stdlogicvector/modularCamera_hw/Sensor_HallArray_Ctrl.brd

## EAGLE design Sensor_HallArray_Ctrl.brd (2026-06-28)

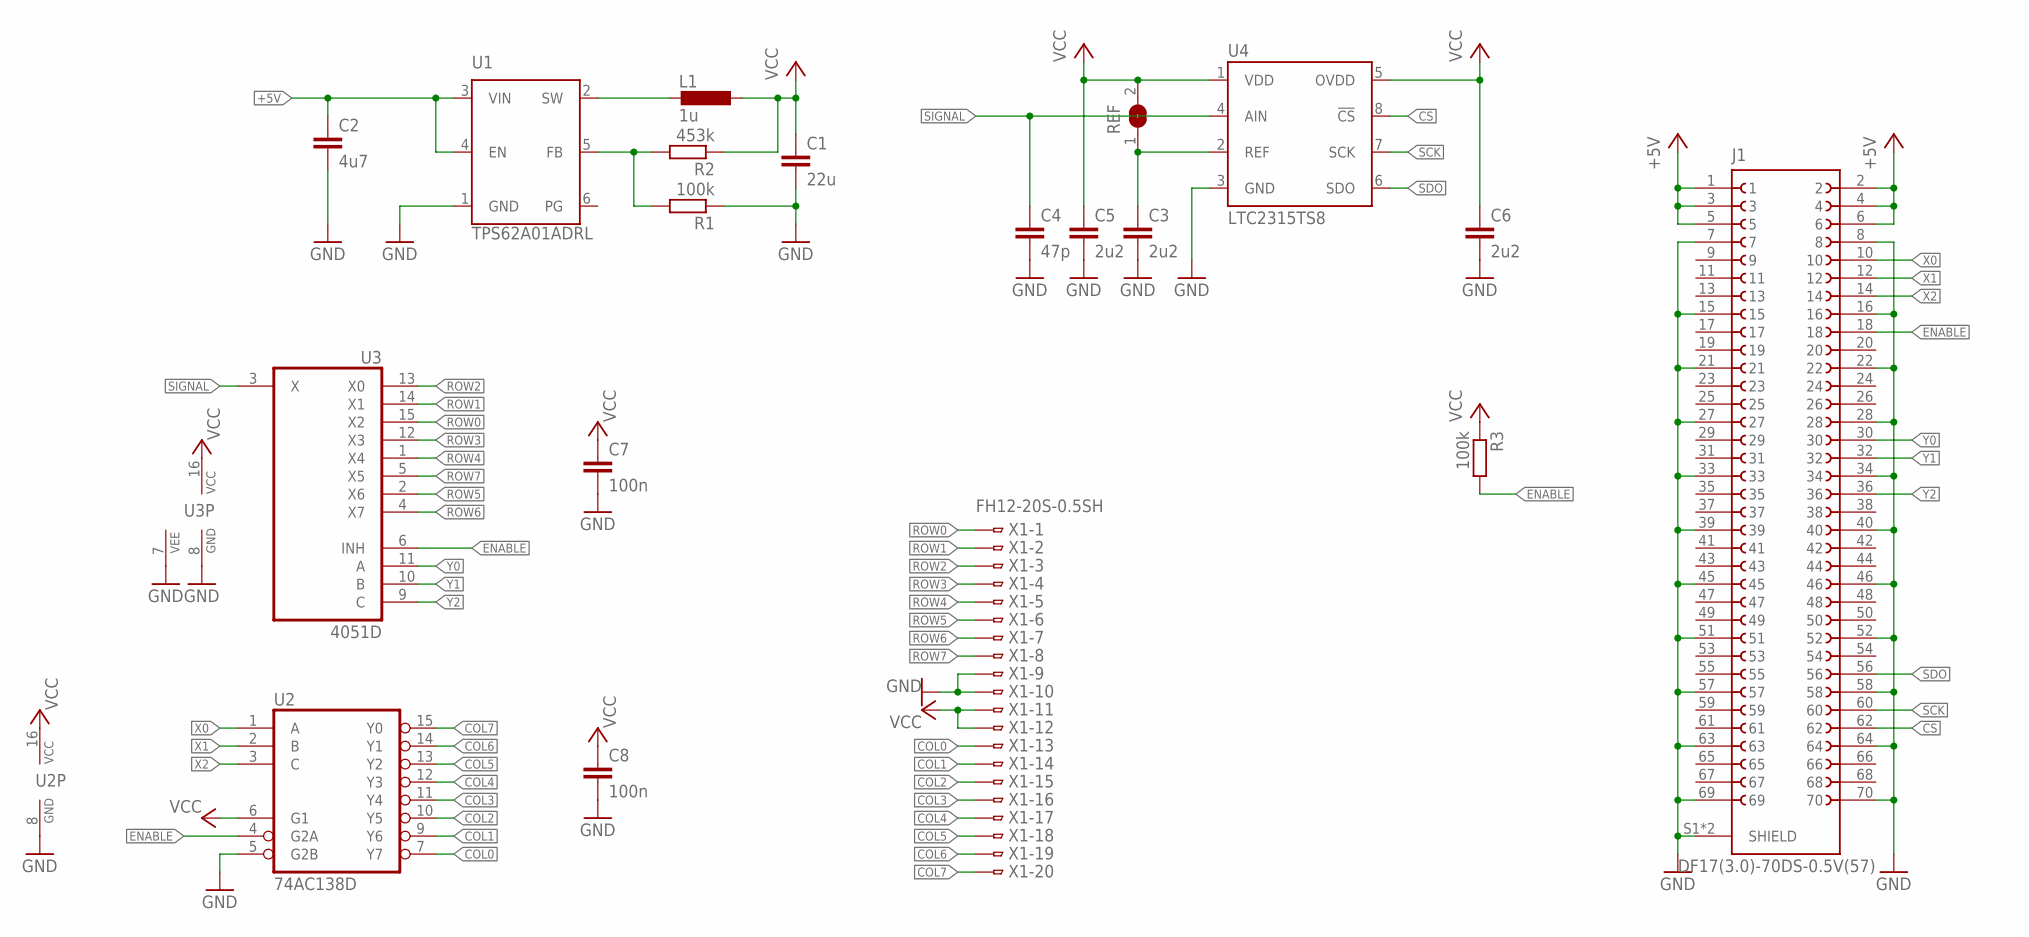
[picture p45: schematic Sensor_HallArray_Ctrl.sch]

Parts:
C1: 22u; C0603; LCSC C109448
C2: 4u7; C0603; LCSC C19666
C3, C5, C6: 2u2; C0603; LCSC C19666
C4: 47p; C0402
C7, C8: 100n; C0402
J1: DF17(3.0)-70DS-0.5V(57)
L1: 1u; L1008; MPN LQM2HPN1R0MG0L; DIGIKEY 490-5112-1-ND
R1, R3: 100k; R0402; DIGIKEY RMCF0402FT100KCT-ND
R2: 453k; R0402; LCSC C137978
REF: SJ
U1: TPS62A01ADRL; SOTFL50P160X60-6N; DIGIKEY 296-TPS62A01ADRLRCT-ND
U2: 74AC138D; SO16
U3: 4051D; SO16
U4: LTC2315TS8; SOT23-8L
X1: FH12-20S-0.5SH

Connections:
!CS: J1.62, U4.8 (!CS)
!ENABLE: J1.18, R3.2, U2.4 (G2A), U3.6 (INH)
+5V: C2.1, J1.1, J1.2, J1.3, J1.4, J1.5, J1.6, U1.3 (VIN), U1.4 (EN)
COL0: U2.7 (Y7), X1.13
COL1: U2.9 (Y6), X1.14
COL2: U2.10 (Y5), X1.15
COL3: U2.11 (Y4), X1.16
COL4: U2.12 (Y3), X1.17
COL5: U2.13 (Y2), X1.18
COL6: U2.14 (Y1), X1.19
COL7: U2.15 (Y0), X1.20
GND: C1.2, C2.2, C3.2, C4.2, C5.2, C6.2, C7.2, C8.2, J1.7, J1.8, J1.15, J1.16, J1.21, J1.22, J1.27, J1.28, J1.33, J1.34, J1.39, J1.40, J1.45, J1.46, J1.51, J1.52, J1.57, J1.58, J1.63, J1.64, J1.69, J1.70, J1.S1 (SHIELD), J1.S2 (SHIELD), R1.1, U1.1 (GND), U2.5 (G2B), U2.8 (GND), U3.7 (VEE), U3.8 (GND), U4.3 (GND), X1.9, X1.10
unnamed: R1.2, R2.2, U1.5 (FB)
unnamed: L1.2, U1.2 (SW)
unnamed: C3.1, REF.1, U4.2 (REF)
ROW0: U3.15 (X2), X1.1
ROW1: U3.14 (X1), X1.2
ROW2: U3.13 (X0), X1.3
ROW3: U3.12 (X3), X1.4
ROW4: U3.1 (X4), X1.5
ROW5: U3.2 (X6), X1.6
ROW6: U3.4 (X7), X1.7
ROW7: U3.5 (X5), X1.8
SCK: J1.60, U4.7 (SCK)
SDO: J1.56, U4.6 (SDO)
SIGNAL: C4.1, U3.3 (X), U4.4 (AIN)
VCC: C1.1, C5.1, C6.1, C7.1, C8.1, L1.1, R2.1, R3.1, REF.2, U2.6 (G1), U2.16 (VCC), U3.16 (VCC), U4.1 (VDD), U4.5 (OVDD), X1.11, X1.12
X0: J1.10, U2.1 (A)
X1: J1.12, U2.2 (B)
X2: J1.14, U2.3 (C)
Y0: J1.30, U3.11 (A)
Y1: J1.32, U3.10 (B)
Y2: J1.36, U3.9 (C)

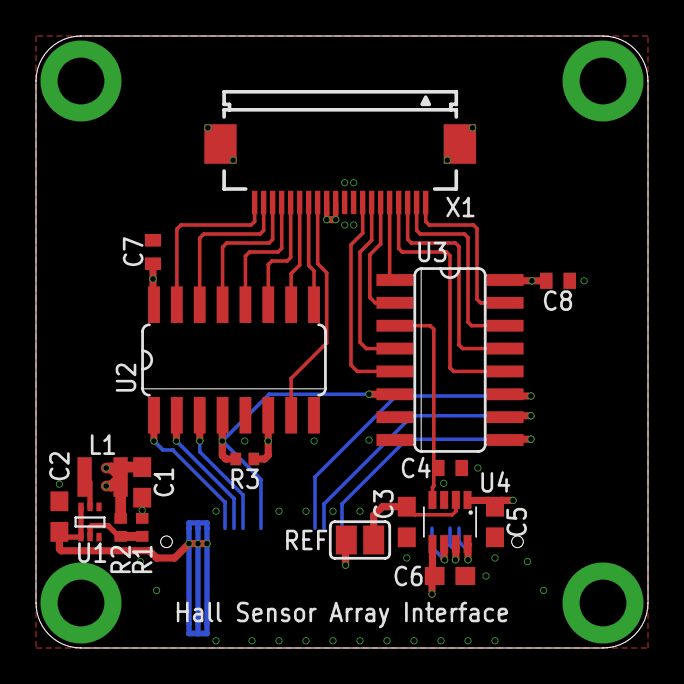
[picture p46: board Sensor_HallArray_Ctrl.brd from above]

Board: 4 copper layers, 34.0 x 34.0 mm, 19 parts (1 on the bottom side), 33 nets.
