stdlogicvector/modularCamera_hw/Sensor_Cameralink_TRX.brd

## EAGLE design Sensor_Cameralink_TRX.brd (2026-06-28)

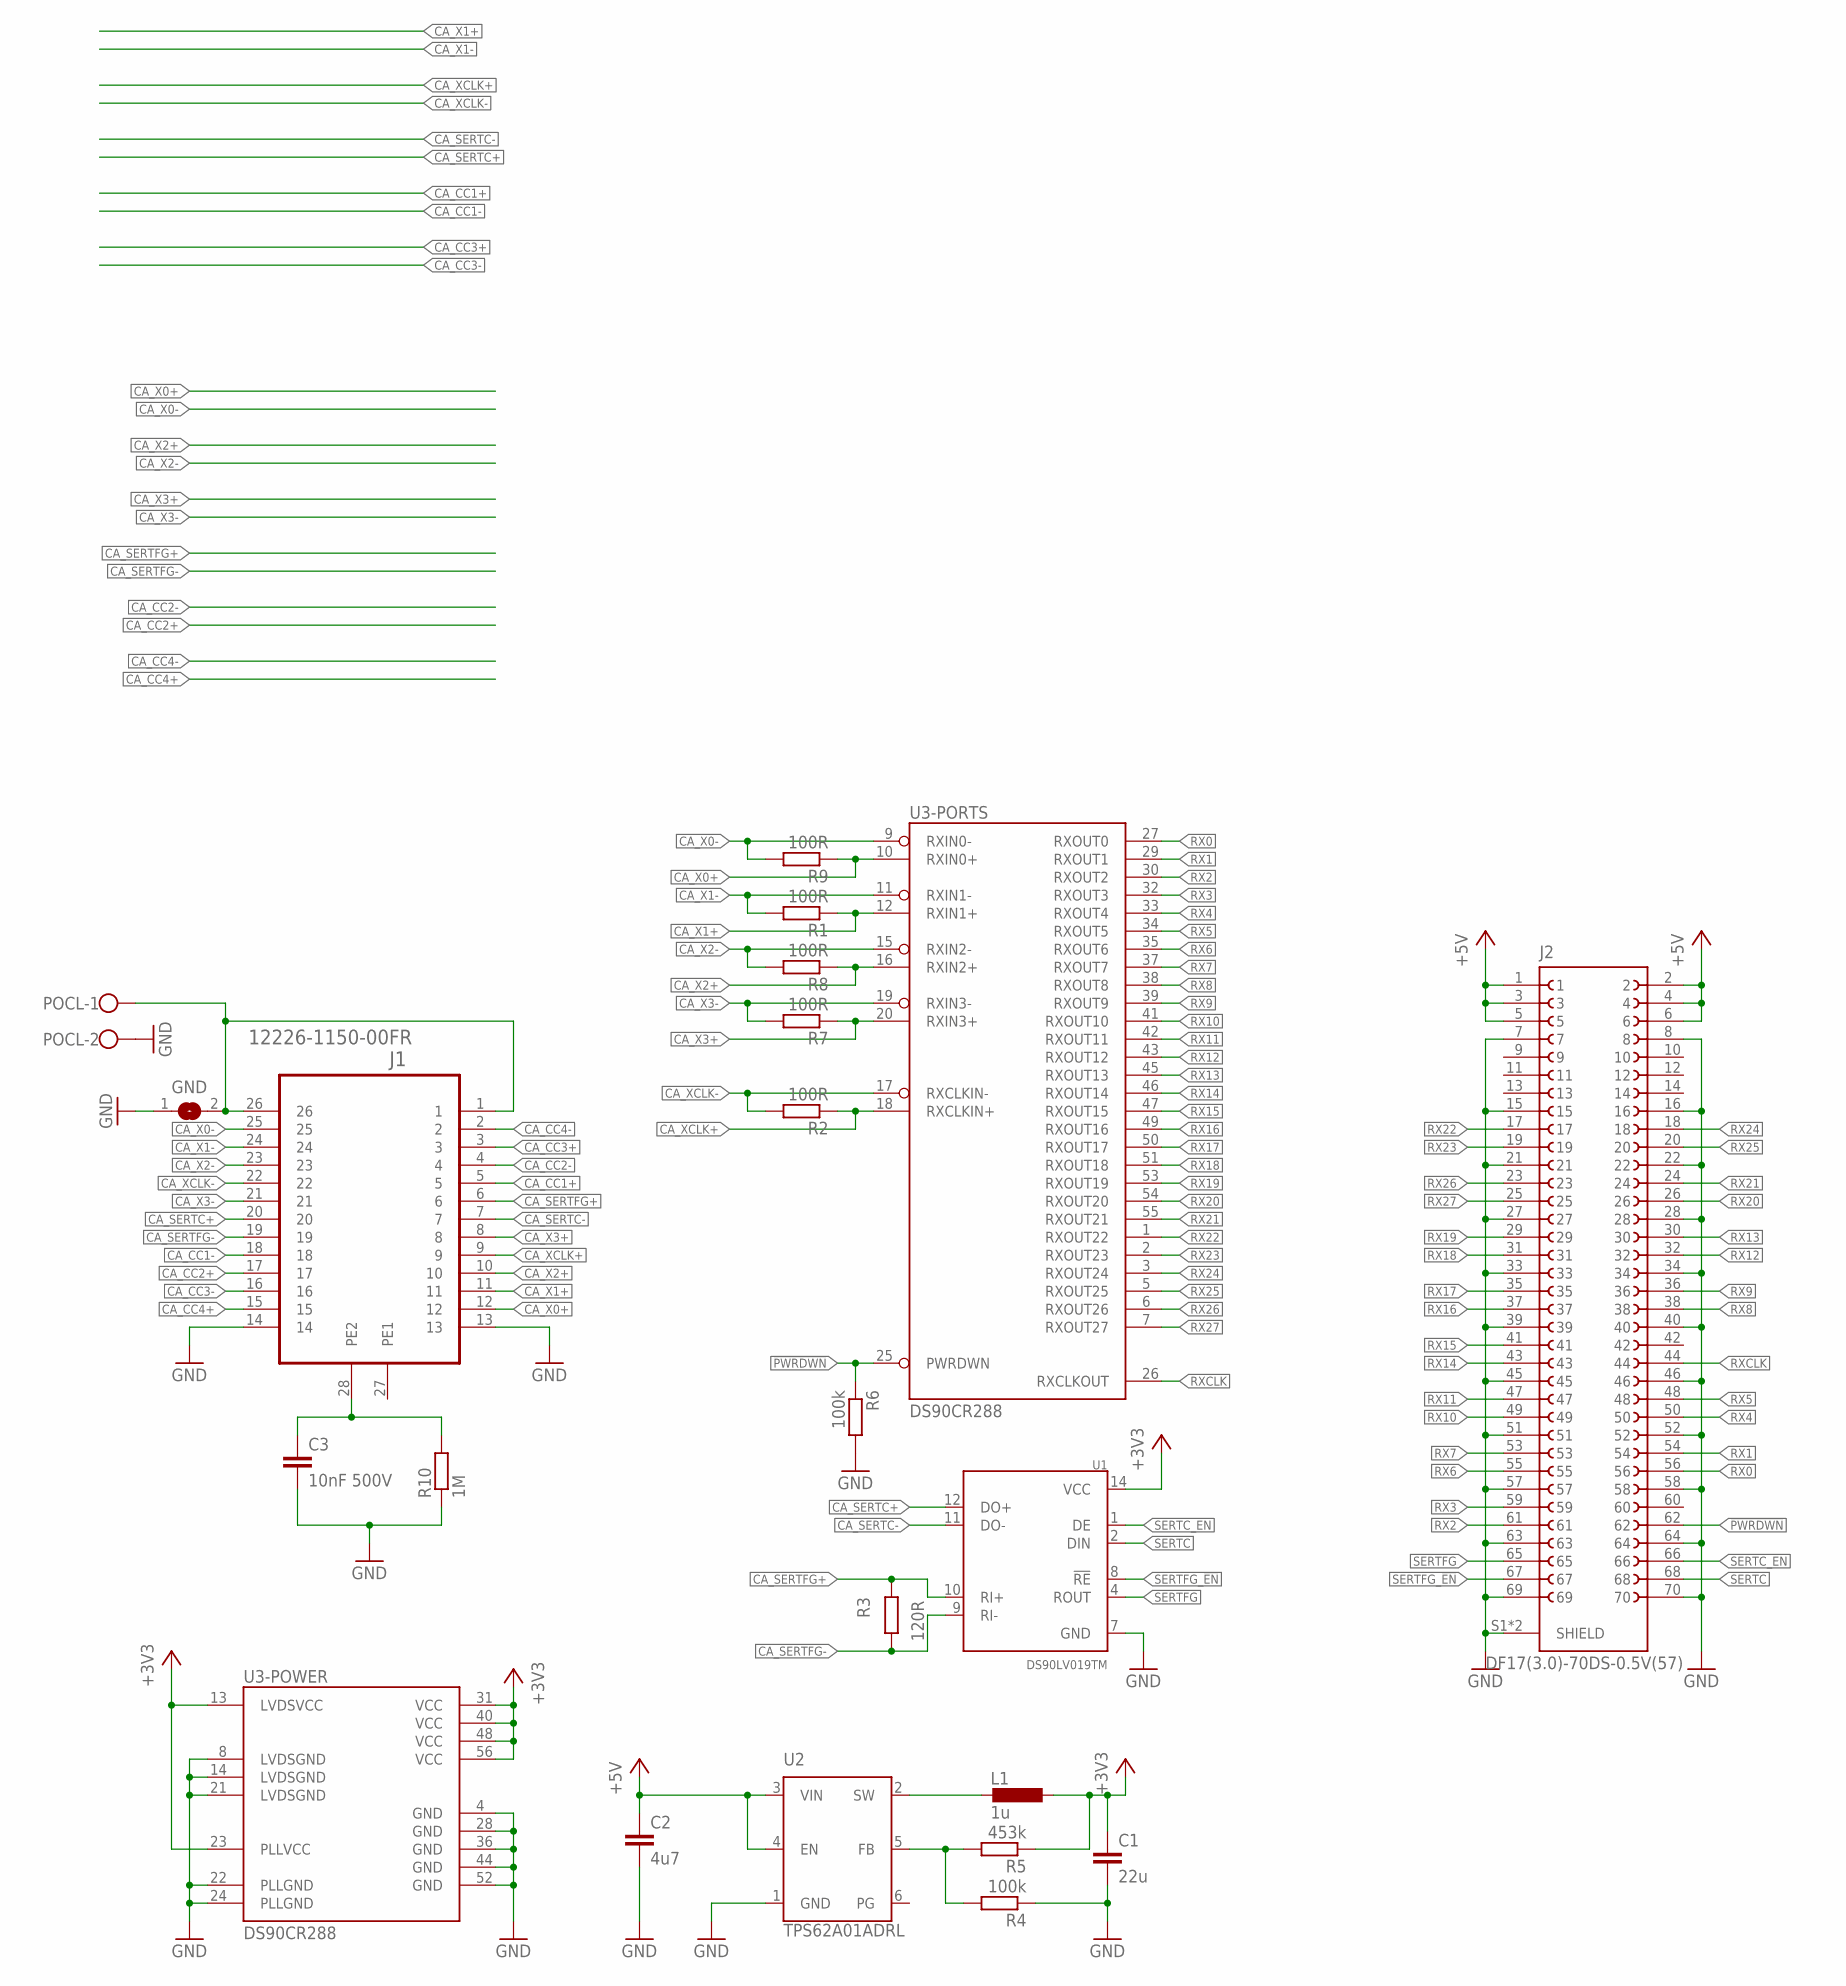
[picture p47: schematic Sensor_Cameralink_TRX.sch]

Parts:
C1: 22u; C0603; LCSC C109448
C2: 4u7; C0603; LCSC C19666
C3: 10nF 500V; C0805
GND: SJ
J1: 12226-1150-00FR; 3M_12226-1150-00FR
J2: DF17(3.0)-70DS-0.5V(57)
L1: 1u; L1008; MPN LQM2HPN1R0MG0L; DIGIKEY 490-5112-1-ND
POCL: W237-102
R1, R2, R7, R8, R9: 100R; R0402
R3: 120R; R0402
R4, R6: 100k; R0402; DIGIKEY RMCF0402FT100KCT-ND
R5: 453k; R0402; LCSC C137978
R10: 1M; R0805
U1: DS90LV019TM; SO-14
U2: TPS62A01ADRL; SOTFL50P160X60-6N; DIGIKEY 296-TPS62A01ADRLRCT-ND
U3: DS90CR288; HTSSOP56

Connections:
!PWRDWN: J2.62, R6.1, U3.25 (PWRDWN)
+3V3: C1.1, L1.1, R5.1, U1.14 (VCC), U3.13 (LVDSVCC), U3.23 (PLLVCC), U3.31 (VCC), U3.40 (VCC), U3.48 (VCC), U3.56 (VCC)
+5V: C2.1, J2.1, J2.2, J2.3, J2.4, J2.5, J2.6, U2.3 (VIN), U2.4 (EN)
CA_CC1+: J1.5
CA_CC1-: J1.18
CA_CC2+: J1.17
CA_CC2-: J1.4
CA_CC3+: J1.3
CA_CC3-: J1.16
CA_CC4+: J1.15
CA_CC4-: J1.2
CA_SERTC+: J1.20, U1.12 (DO+)
CA_SERTC-: J1.7, U1.11 (DO-)
CA_SERTFG+: J1.6, R3.1, U1.10 (RI+)
CA_SERTFG-: J1.19, R3.2, U1.9 (RI-)
CA_X0+: J1.12, R9.1, U3.10 (RXIN0+)
CA_X0-: J1.25, R9.2, U3.9 (RXIN0-)
CA_X1+: J1.11, R1.1, U3.12 (RXIN1+)
CA_X1-: J1.24, R1.2, U3.11 (RXIN1-)
CA_X2+: J1.10, R8.1, U3.16 (RXIN2+)
CA_X2-: J1.23, R8.2, U3.15 (RXIN2-)
CA_X3+: J1.8, R7.1, U3.20 (RXIN3+)
CA_X3-: J1.21, R7.2, U3.19 (RXIN3-)
CA_XCLK+: J1.9, R2.1, U3.18 (RXCLKIN+)
CA_XCLK-: J1.22, R2.2, U3.17 (RXCLKIN-)
GND: C1.2, C2.2, C3.2, GND.1, J1.13, J1.14, J2.7, J2.8, J2.15, J2.16, J2.21, J2.22, J2.27, J2.28, J2.33, J2.34, J2.39, J2.40, J2.45, J2.46, J2.51, J2.52, J2.57, J2.58, J2.63, J2.64, J2.69, J2.70, J2.S1 (SHIELD), J2.S2 (SHIELD), POCL.2, R4.1, R6.2, R10.1, U1.7 (GND), U2.1 (GND), U3.4 (GND), U3.8 (LVDSGND), U3.14 (LVDSGND), U3.21 (LVDSGND), U3.22 (PLLGND), U3.24 (PLLGND), U3.28 (GND), U3.36 (GND), U3.44 (GND), U3.52 (GND)
unnamed: C3.1, J1.28 (PE2), R10.2
unnamed: GND.2, J1.1, J1.26, POCL.1
unnamed: R4.2, R5.2, U2.5 (FB)
unnamed: L1.2, U2.2 (SW)
RX0: J2.56, U3.27 (RXOUT0)
RX1: J2.54, U3.29 (RXOUT1)
RX2: J2.61, U3.30 (RXOUT2)
RX3: J2.59, U3.32 (RXOUT3)
RX4: J2.50, U3.33 (RXOUT4)
RX5: J2.48, U3.34 (RXOUT5)
RX6: J2.55, U3.35 (RXOUT6)
RX7: J2.53, U3.37 (RXOUT7)
RX8: J2.38, U3.38 (RXOUT8)
RX9: J2.36, U3.39 (RXOUT9)
RX10: J2.49, U3.41 (RXOUT10)
RX11: J2.47, U3.42 (RXOUT11)
RX12: J2.32, U3.43 (RXOUT12)
RX13: J2.30, U3.45 (RXOUT13)
RX14: J2.43, U3.46 (RXOUT14)
RX15: J2.41, U3.47 (RXOUT15)
RX16: J2.37, U3.49 (RXOUT16)
RX17: J2.35, U3.50 (RXOUT17)
RX18: J2.31, U3.51 (RXOUT18)
RX19: J2.29, U3.53 (RXOUT19)
RX20: J2.26, U3.54 (RXOUT20)
RX21: J2.24, U3.55 (RXOUT21)
RX22: J2.17, U3.1 (RXOUT22)
RX23: J2.19, U3.2 (RXOUT23)
RX24: J2.18, U3.3 (RXOUT24)
RX25: J2.20, U3.5 (RXOUT25)
RX26: J2.23, U3.6 (RXOUT26)
RX27: J2.25, U3.7 (RXOUT27)
RXCLK: J2.44, U3.26 (RXCLKOUT)
SERTC: J2.68, U1.2 (DIN)
SERTC_EN: J2.66, U1.1 (DE)
SERTFG: J2.65, U1.4 (ROUT)
SERTFG_!EN: J2.67, U1.8 (!RE)

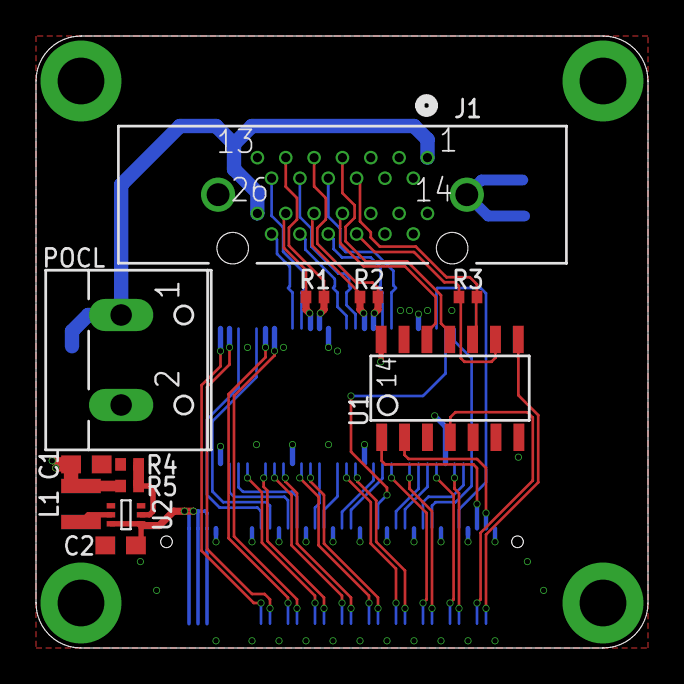
[picture p48: board Sensor_Cameralink_TRX.brd from above]

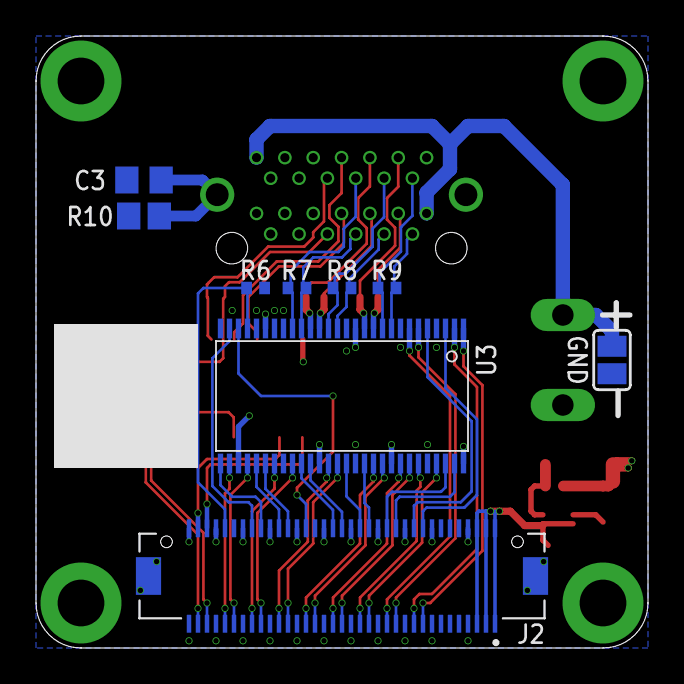
[picture p49: board Sensor_Cameralink_TRX.brd from below]

Board: 4 copper layers, 34.0 x 34.0 mm, 21 parts (9 on the bottom side), 55 nets.
