stdlogicvector/modularCamera_hw/Sensor_MT9P.brd

## EAGLE design Sensor_MT9P.brd (2026-06-28)

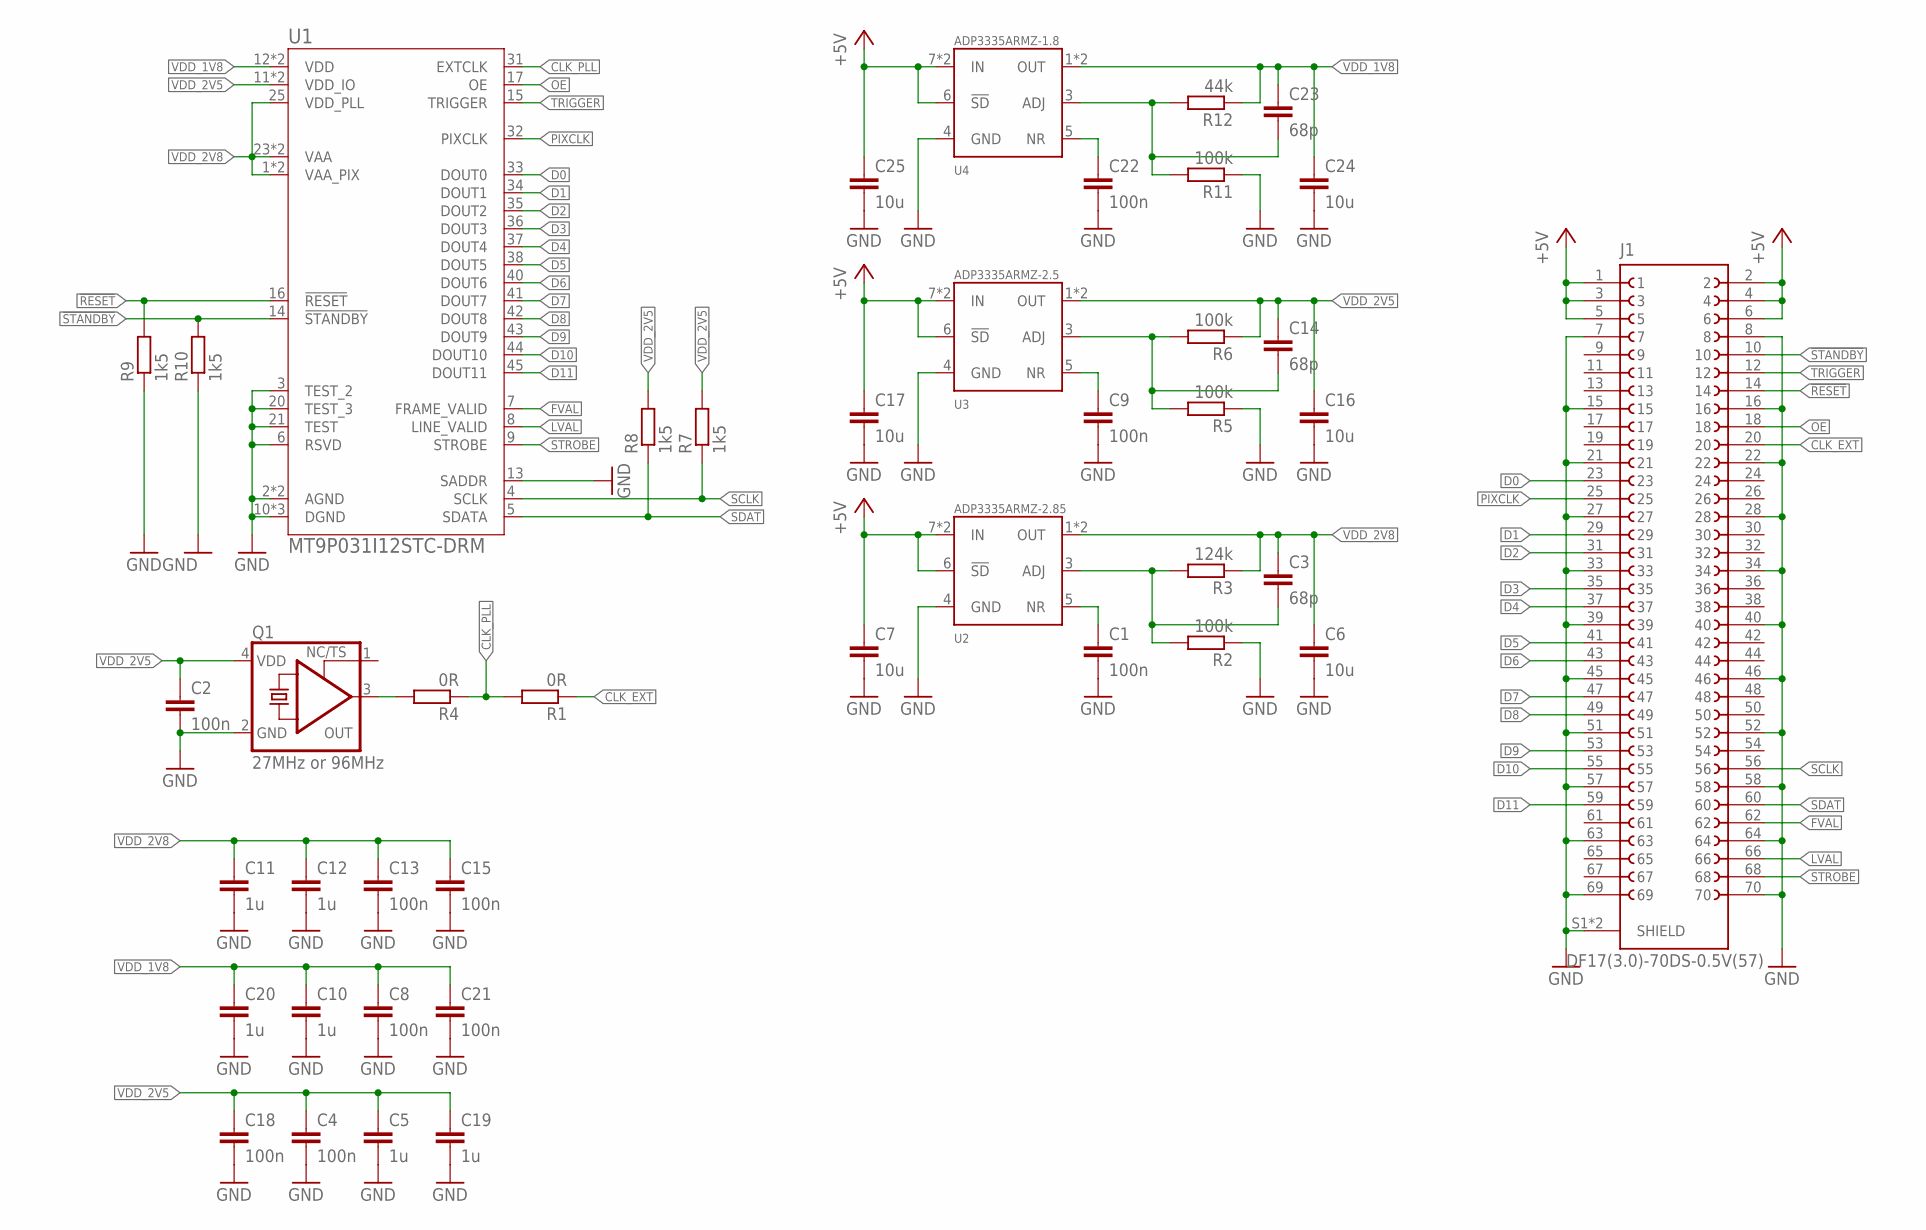
[picture p50: schematic Sensor_MT9P.sch]

Parts:
C1, C2, C4, C8, C9, C13, C15, C18, C21, C22: 100n; C0402; LCSC C1525
C3, C14, C23: 68p; C0402; LCSC C1525
C5, C10, C11, C12, C19, C20: 1u; C0402
C6, C7, C16, C17, C24, C25: 10u; C0603
J1: DF17(3.0)-70DS-0.5V(57)
Q1: 27MHz or 96MHz; 3.2X2.5_KXO-V96
R1, R4: 0R; R0402
R2, R5, R6, R11: 100k; R0402
R3: 124k; R0402
R7, R8, R9, R10: 1k5; R0402
R12: 44k; R0402
U1: MT9P031I12STC-DRM; ILCC48_10X10_847AA-O_OSI-M
U2: ADP3335ARMZ-2.85; MSOP08; DIGIKEY 505-ADP3335ARMZ-3.3RL7CT-ND
U3: ADP3335ARMZ-2.5; MSOP08; DIGIKEY 505-ADP3335ARMZ-2.5-RLCT-ND
U4: ADP3335ARMZ-1.8; MSOP08; DIGIKEY 505-ADP3335ARMZ-1.8-R7CT-ND

Connections:
!RESET: J1.14, R9.2, U1.16 (!RESET)
!STANDBY: J1.10, R10.2, U1.14 (!STANDBY)
+5V: C7.1, C17.1, C25.1, J1.1, J1.2, J1.3, J1.4, J1.5, J1.6, U2.6 (!SD), U2.7 (IN), U2.8 (IN), U3.6 (!SD), U3.7 (IN), U3.8 (IN), U4.6 (!SD), U4.7 (IN), U4.8 (IN)
CLK: Q1.3 (OUT), R4.2
CLK_EXT: J1.20, R1.1
CLK_PLL: R1.2, R4.1, U1.31 (EXTCLK)
D0: J1.23, U1.33 (DOUT0)
D1: J1.29, U1.34 (DOUT1)
D2: J1.31, U1.35 (DOUT2)
D3: J1.35, U1.36 (DOUT3)
D4: J1.37, U1.37 (DOUT4)
D5: J1.41, U1.38 (DOUT5)
D6: J1.43, U1.40 (DOUT6)
D7: J1.47, U1.41 (DOUT7)
D8: J1.49, U1.42 (DOUT8)
D9: J1.53, U1.43 (DOUT9)
D10: J1.55, U1.44 (DOUT10)
D11: J1.59, U1.45 (DOUT11)
FVAL: J1.62, U1.7 (FRAME_VALID)
GND: C1.2, C2.2, C4.2, C5.2, C6.2, C7.2, C8.2, C9.2, C10.2, C11.2, C12.2, C13.2, C15.2, C16.2, C17.2, C18.2, C19.2, C20.2, C21.2, C22.2, C24.2, C25.2, J1.7, J1.8, J1.15, J1.16, J1.21, J1.22, J1.27, J1.28, J1.33, J1.34, J1.39, J1.40, J1.45, J1.46, J1.51, J1.52, J1.57, J1.58, J1.63, J1.64, J1.69, J1.70, J1.S1 (SHIELD), J1.S2 (SHIELD), Q1.2 (GND), R2.1, R5.1, R9.1, R10.1, R11.1, U1.2 (AGND), U1.3 (TEST_2), U1.6 (RSVD), U1.10 (DGND), U1.13 (SADDR), U1.20 (TEST_3), U1.21 (TEST), U1.22 (AGND), U1.26 (DGND), U1.46 (DGND), U2.4 (GND), U3.4 (GND), U4.4 (GND)
LVAL: J1.66, U1.8 (LINE_VALID)
unnamed: C1.1, U2.5 (NR)
unnamed: C22.1, U4.5 (NR)
unnamed: C9.1, U3.5 (NR)
unnamed: C23.2, R11.2, R12.2, U4.3 (ADJ)
unnamed: C14.2, R5.2, R6.2, U3.3 (ADJ)
unnamed: C3.2, R2.2, R3.2, U2.3 (ADJ)
OE: J1.18, U1.17 (OE)
PIXCLK: J1.25, U1.32 (PIXCLK)
SCLK: J1.56, R7.1, U1.4 (SCLK)
SDAT: J1.60, R8.1, U1.5 (SDATA)
STROBE: J1.68, U1.9 (STROBE)
TRIGGER: J1.12, U1.15 (TRIGGER)
VDD_1V8: C8.1, C10.1, C20.1, C21.1, C23.1, C24.1, R12.1, U1.12 (VDD), U1.47 (VDD), U4.1 (OUT), U4.2 (OUT)
VDD_2V5: C2.1, C4.1, C5.1, C14.1, C16.1, C18.1, C19.1, Q1.4 (VDD), R6.1, R7.2, R8.2, U1.11 (VDD_IO), U1.39 (VDD_IO), U3.1 (OUT), U3.2 (OUT)
VDD_2V8: C3.1, C6.1, C11.1, C12.1, C13.1, C15.1, R3.1, U1.1 (VAA_PIX), U1.23 (VAA), U1.24 (VAA), U1.25 (VDD_PLL), U1.48 (VAA_PIX), U2.1 (OUT), U2.2 (OUT)

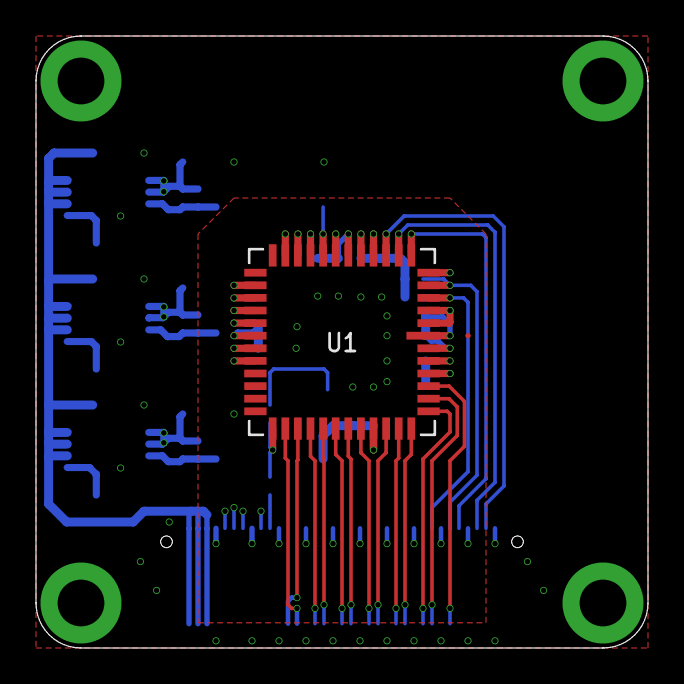
[picture p51: board Sensor_MT9P.brd from above]

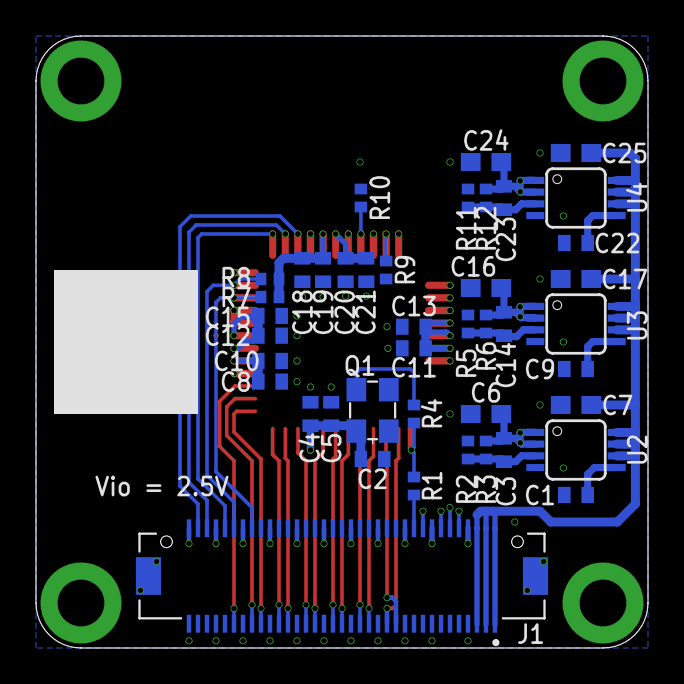
[picture p52: board Sensor_MT9P.brd from below]

Board: 4 copper layers, 34.0 x 34.0 mm, 43 parts (42 on the bottom side), 36 nets.
