stdlogicvector/modularCamera_hw/Sensor_AnalogVideo.brd

## EAGLE design Sensor_AnalogVideo.brd (2026-06-28)

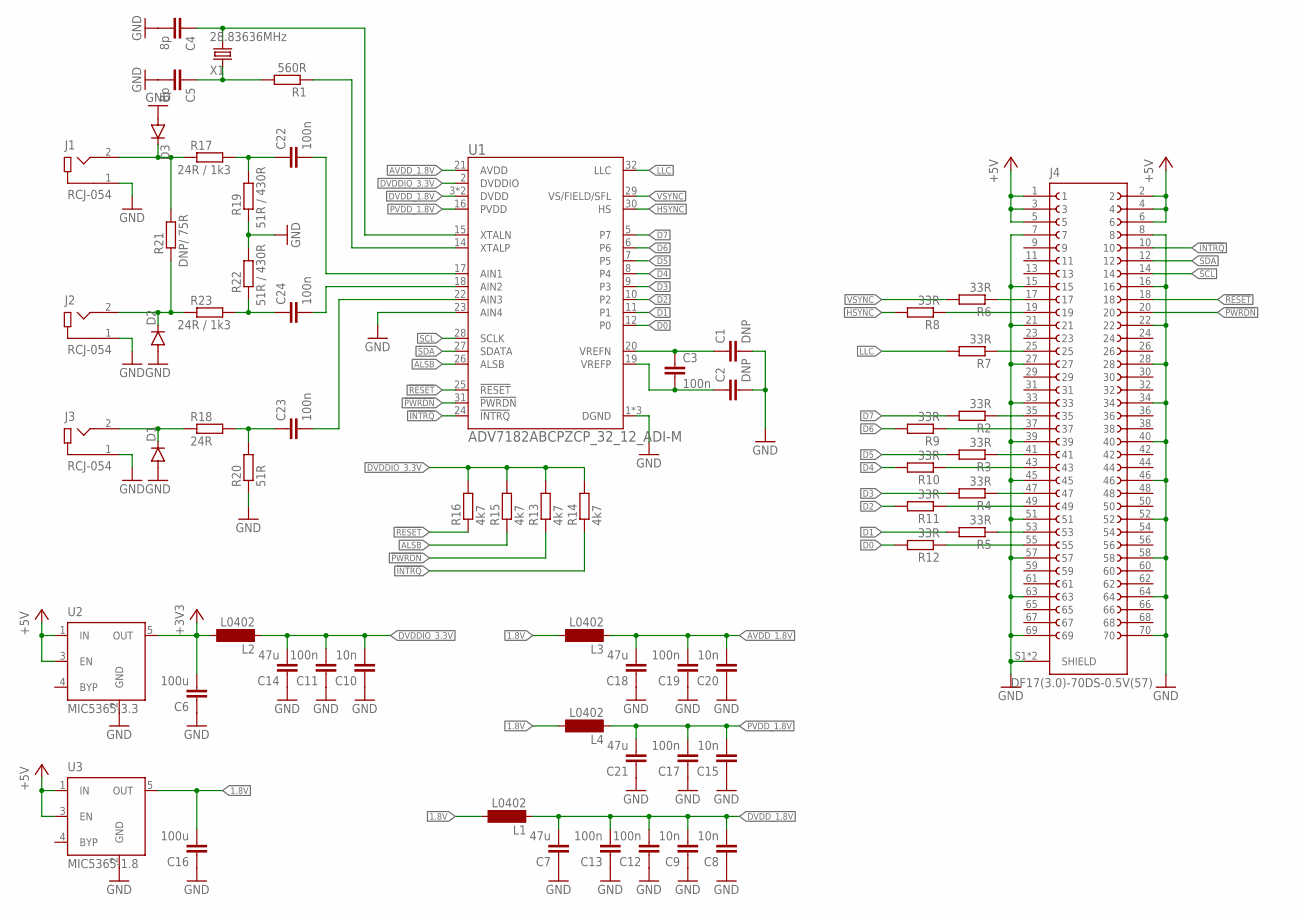
[picture p53: schematic Sensor_AnalogVideo.sch]

Parts:
C1, C2: DNP; C0402
C3, C11, C12, C13, C17, C19, C22, C23, C24: 100n; C0402; LCSC C1525
C4, C5: 8p; C0402; LCSC C281765
C6, C16: 100u; C1206; DIGIKEY 490-GRM31CD80J107MEA8LCT-ND
C7, C14, C18, C21: 47u; C0805; LCSC C77072
C8, C9, C10, C15, C20: 10n; C0402; LCSC C15195
D1, D2, D3: DIODE-SOD323-W; SOD323-W
J1, J2, J3: RCJ-054; CUI_RCJ-054; DIGIKEY CP-1427-ND
J4: DF17(3.0)-70DS-0.5V(57)
L1, L2, L3, L4: L0402; C0402; LCSC C88970
R1: 560R; R0402
R2, R3, R4, R5, R6, R7, R8, R9, R10, R11, R12: 33R; R0402
R13, R14, R15, R16: 4k7; R0402; LCSC C25900
R17, R23: 24R / 1k3; R0603
R18: 24R; R0603
R19, R22: 51R / 430R; R0603
R20: 51R; R0603
R21: DNP/ 75R; R0603
U1: ADV7182ABCPZCP_32_12_ADI-M; CP_32_12_ADI-M; DIGIKEY 505-ADV7182ABCPZ-ND
U2: MIC5365-3.3; SOT23-5; DIGIKEY 576-4085-1-ND
U3: MIC5365-1.8; SOT23-5; DIGIKEY 576-4082-1-ND
X1: 28.83636MHz; 2520; DIGIKEY XC3048CT-ND

Connections:
1.8V: C16.1, L1.2, L3.2, L4.2, U3.5 (OUT)
!INTRQ: J4.10, R14.1, U1.24 (!INTRQ)
!PWRDN: J4.20, R13.1, U1.31 (!PWRDN)
!RESET: J4.18, R16.1, U1.25 (!RESET)
+3V3: C6.1, L2.2, U2.5 (OUT)
+5V: J4.1, J4.2, J4.3, J4.4, J4.5, J4.6, U2.1 (IN), U2.3 (EN), U3.1 (IN), U3.3 (EN)
ALSB: R15.1, U1.26 (ALSB)
AVDD_1.8V: C18.2, C19.2, C20.2, L3.1, U1.21 (AVDD)
D0: R12.2, U1.12 (P0)
D1: R5.2, U1.11 (P1)
D2: R11.2, U1.10 (P2)
D3: R4.2, U1.9 (P3)
D4: R10.2, U1.8 (P4)
D5: R3.2, U1.7 (P5)
D6: R9.2, U1.6
D7: R2.2, U1.5 (P7)
DVDDIO_3.3V: C10.2, C11.2, C14.2, L2.1, R13.2, R14.2, R15.2, R16.2, U1.2 (DVDDIO)
DVDD_1.8V: C7.2, C8.2, C9.2, C12.2, C13.2, L1.1, U1.3 (DVDD), U1.13 (DVDD)
GND: C1.2, C2.2, C4.2, C5.2, C6.2, C7.1, C8.1, C9.1, C10.1, C11.1, C12.1, C13.1, C14.1, C15.1, C16.2, C17.1, C18.1, C19.1, C20.1, C21.1, D1.A, D2.A, D3.A, J1.1, J2.1, J3.1, J4.7, J4.8, J4.15, J4.16, J4.21, J4.22, J4.27, J4.28, J4.33, J4.34, J4.39, J4.40, J4.45, J4.46, J4.51, J4.52, J4.57, J4.58, J4.63, J4.64, J4.69, J4.70, J4.S1 (SHIELD), J4.S2 (SHIELD), R19.1, R20.1, R22.2, U1.1 (DGND), U1.4 (DGND), U1.23 (AIN4), U1.33 (DGND), U2.2 (GND), U3.2 (GND)
HSYNC: R8.2, U1.30 (HS)
LLC: R7.2, U1.32 (LLC)
unnamed: C1.1, C3.1, U1.20 (VREFN)
unnamed: C2.1, C3.2, U1.19 (VREFP)
unnamed: D3.C, J1.2, R17.1, R21.2
unnamed: D2.C, J2.2, R21.1, R23.1
unnamed: C22.1, R17.2, R19.2
unnamed: C24.1, R22.1, R23.2
unnamed: C22.2, U1.17 (AIN1)
unnamed: C24.2, U1.18 (AIN2)
unnamed: D1.C, J3.2, R18.1
unnamed: C23.2, U1.22 (AIN3)
unnamed: C23.1, R18.2, R20.2
unnamed: J4.17, R6.1
unnamed: J4.19, R8.1
unnamed: J4.25, R7.1
unnamed: J4.35, R2.1
unnamed: J4.37, R9.1
unnamed: J4.41, R3.1
unnamed: J4.43, R10.1
unnamed: J4.47, R4.1
unnamed: J4.49, R11.1
unnamed: J4.53, R5.1
unnamed: J4.55, R12.1
unnamed: R1.1, U1.14 (XTALP)
PVDD_1.8V: C15.2, C17.2, C21.2, L4.1, U1.16 (PVDD)
SCL: J4.14, U1.28 (SCLK)
SDA: J4.12, U1.27 (SDATA)
VSYNC: R6.2, U1.29 (VS/FIELD/SFL)
XTAL_IN: C4.1, U1.15 (XTALN), X1.1
XTAL_OUT: C5.1, R1.2, X1.3 (2)

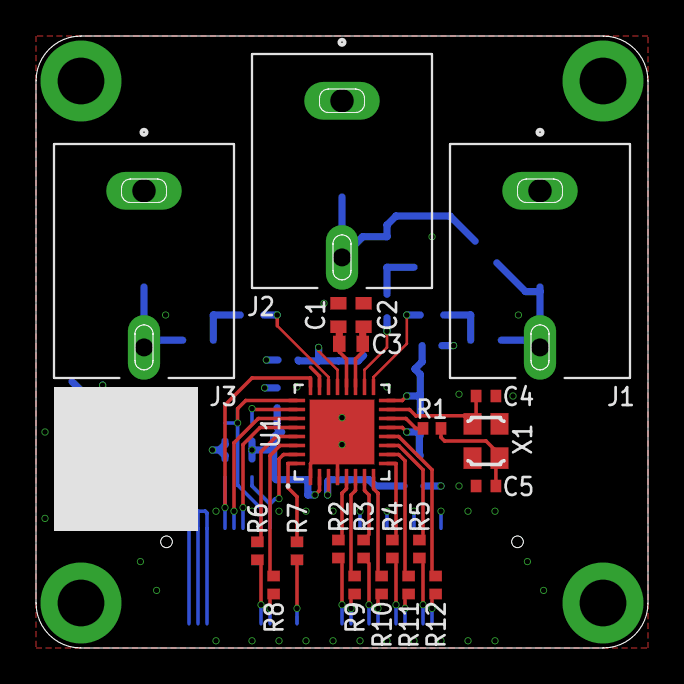
[picture p54: board Sensor_AnalogVideo.brd from above]

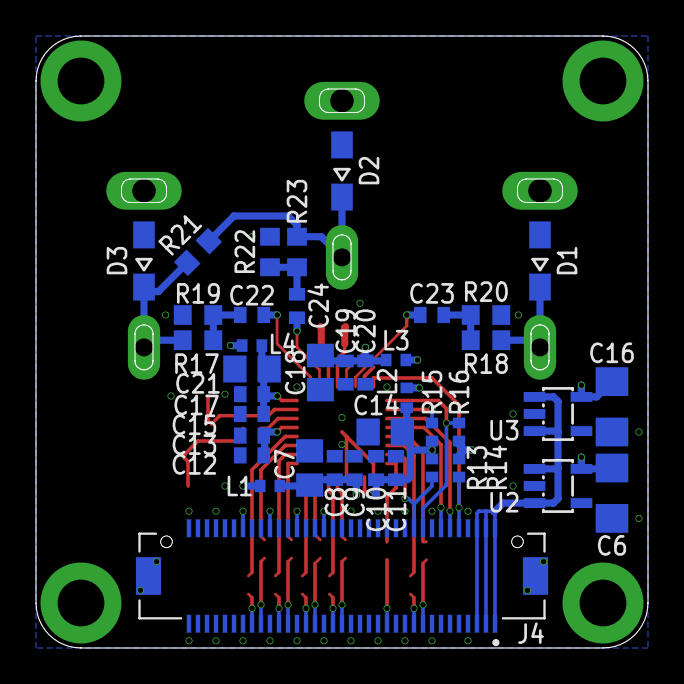
[picture p55: board Sensor_AnalogVideo.brd from below]

Board: 4 copper layers, 34.0 x 34.0 mm, 62 parts (40 on the bottom side), 50 nets.
