stdlogicvector/modularCamera_hw/Sensor_HallArray_StandAlone_2mm.brd

## EAGLE design Sensor_HallArray_StandAlone_2mm.brd (2026-06-28)

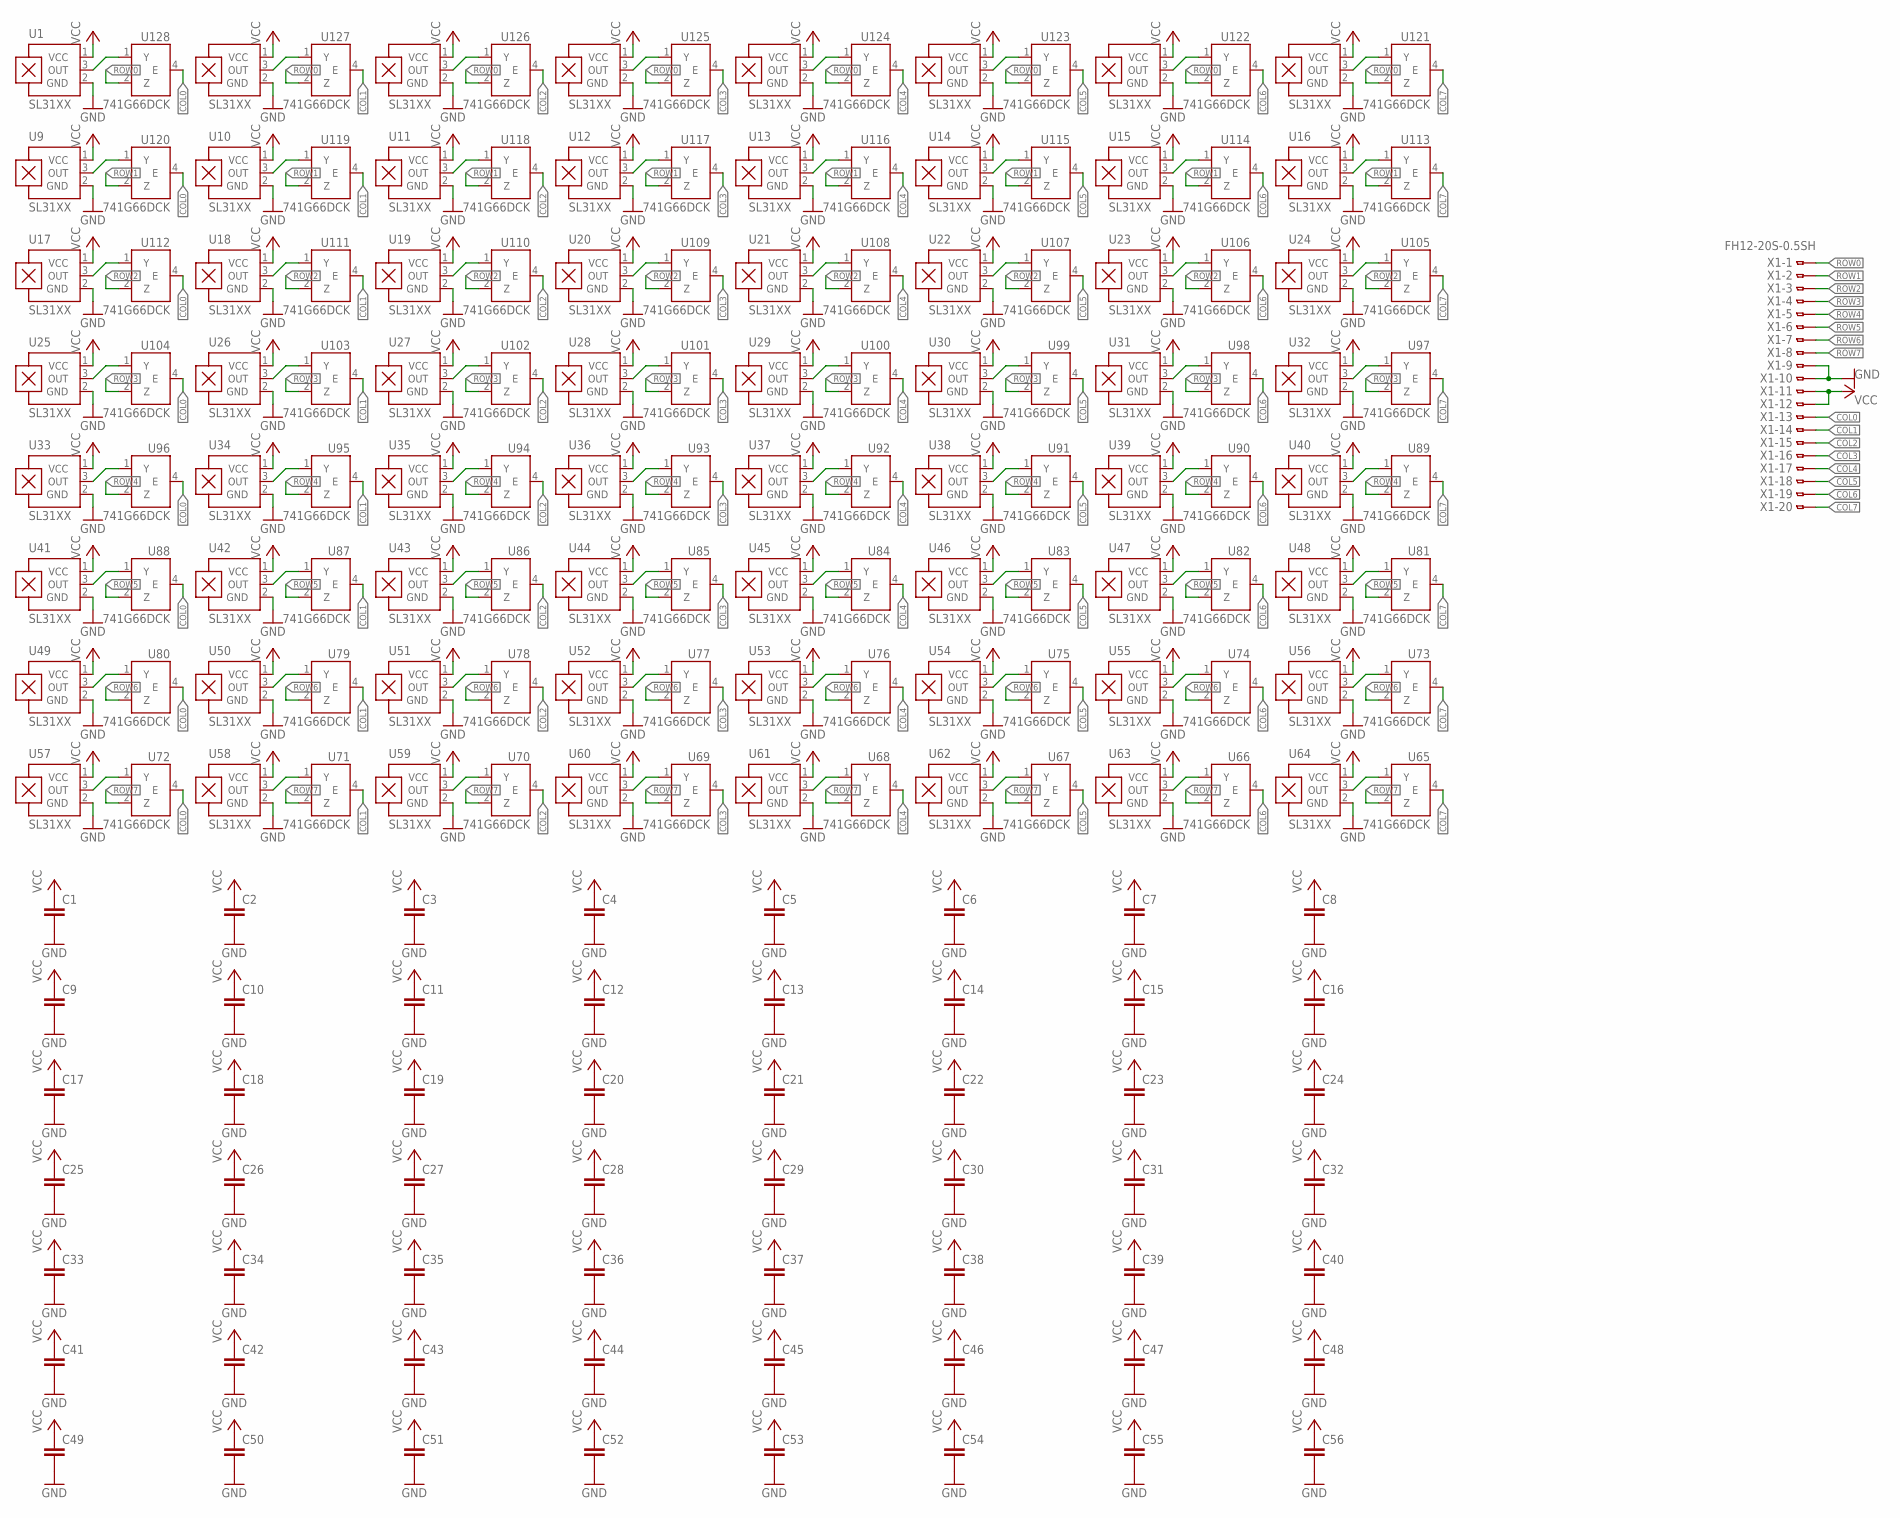
[picture p56: schematic Sensor_HallArray_StandAlone_2mm.sch]

Parts:
C1, C2, C3, C4, C5, C6, C7, C8, C9, C10, C11, C12, C13, C14, C15, C16, C17, C18, C19, C20, C21, C22, C23, C24, C25, C26, C27, C28, C29, C30, C31, C32, C33, C34, C35, C36, C37, C38, C39, C40, C41, C42, C43, C44, C45, C46, C47, C48, C49, C50, C51, C52, C53, C54, C55, C56: C-EUC0201; C0201
U1, U2, U3, U4, U5, U6, U7, U8, U9, U10, U11, U12, U13, U14, U15, U16, U17, U18, U19, U20, U21, U22, U23, U24, U25, U26, U27, U28, U29, U30, U31, U32, U33, U34, U35, U36, U37, U38, U39, U40, U41, U42, U43, U44, U45, U46, U47, U48, U49, U50, U51, U52, U53, U54, U55, U56, U57, U58, U59, U60, U61, U62, U63, U64: SL31XX; SOT1215
U65, U66, U67, U68, U69, U70, U71, U72, U73, U74, U75, U76, U77, U78, U79, U80, U81, U82, U83, U84, U85, U86, U87, U88, U89, U90, U91, U92, U93, U94, U95, U96, U97, U98, U99, U100, U101, U102, U103, U104, U105, U106, U107, U108, U109, U110, U111, U112, U113, U114, U115, U116, U117, U118, U119, U120, U121, U122, U123, U124, U125, U126, U127, U128: 741G66DCK; SC70-5
X1: FH12-20S-0.5SH

Connections:
COL0: U72.4 (E), U80.4 (E), U88.4 (E), U96.4 (E), U104.4 (E), U112.4 (E), U120.4 (E), U128.4 (E), X1.13
COL1: U71.4 (E), U79.4 (E), U87.4 (E), U95.4 (E), U103.4 (E), U111.4 (E), U119.4 (E), U127.4 (E), X1.14
COL2: U70.4 (E), U78.4 (E), U86.4 (E), U94.4 (E), U102.4 (E), U110.4 (E), U118.4 (E), U126.4 (E), X1.15
COL3: U69.4 (E), U77.4 (E), U85.4 (E), U93.4 (E), U101.4 (E), U109.4 (E), U117.4 (E), U125.4 (E), X1.16
COL4: U68.4 (E), U76.4 (E), U84.4 (E), U92.4 (E), U100.4 (E), U108.4 (E), U116.4 (E), U124.4 (E), X1.17
COL5: U67.4 (E), U75.4 (E), U83.4 (E), U91.4 (E), U99.4 (E), U107.4 (E), U115.4 (E), U123.4 (E), X1.18
COL6: U66.4 (E), U74.4 (E), U82.4 (E), U90.4 (E), U98.4 (E), U106.4 (E), U114.4 (E), U122.4 (E), X1.19
COL7: U65.4 (E), U73.4 (E), U81.4 (E), U89.4 (E), U97.4 (E), U105.4 (E), U113.4 (E), U121.4 (E), X1.20
GND: C1.2, C2.2, C3.2, C4.2, C5.2, C6.2, C7.2, C8.2, C9.2, C10.2, C11.2, C12.2, C13.2, C14.2, C15.2, C16.2, C17.2, C18.2, C19.2, C20.2, C21.2, C22.2, C23.2, C24.2, C25.2, C26.2, C27.2, C28.2, C29.2, C30.2, C31.2, C32.2, C33.2, C34.2, C35.2, C36.2, C37.2, C38.2, C39.2, C40.2, C41.2, C42.2, C43.2, C44.2, C45.2, C46.2, C47.2, C48.2, C49.2, C50.2, C51.2, C52.2, C53.2, C54.2, C55.2, C56.2, U1.2 (GND), U2.2 (GND), U3.2 (GND), U4.2 (GND), U5.2 (GND), U6.2 (GND), U7.2 (GND), U8.2 (GND), U9.2 (GND), U10.2 (GND), U11.2 (GND), U12.2 (GND), U13.2 (GND), U14.2 (GND), U15.2 (GND), U16.2 (GND), U17.2 (GND), U18.2 (GND), U19.2 (GND), U20.2 (GND), U21.2 (GND), U22.2 (GND), U23.2 (GND), U24.2 (GND), U25.2 (GND), U26.2 (GND), U27.2 (GND), U28.2 (GND), U29.2 (GND), U30.2 (GND), U31.2 (GND), U32.2 (GND), U33.2 (GND), U34.2 (GND), U35.2 (GND), U36.2 (GND), U37.2 (GND), U38.2 (GND), U39.2 (GND), U40.2 (GND), U41.2 (GND), U42.2 (GND), U43.2 (GND), U44.2 (GND), U45.2 (GND), U46.2 (GND), U47.2 (GND), U48.2 (GND), U49.2 (GND), U50.2 (GND), U51.2 (GND), U52.2 (GND), U53.2 (GND), U54.2 (GND), U55.2 (GND), U56.2 (GND), U57.2 (GND), U58.2 (GND), U59.2 (GND), U60.2 (GND), U61.2 (GND), U62.2 (GND), U63.2 (GND), U64.2 (GND), U65.3 (GND), U66.3 (GND), U67.3 (GND), U68.3 (GND), U69.3 (GND), U70.3 (GND), U71.3 (GND), U72.3 (GND), U73.3 (GND), U74.3 (GND), U75.3 (GND), U76.3 (GND), U77.3 (GND), U78.3 (GND), U79.3 (GND), U80.3 (GND), U81.3 (GND), U82.3 (GND), U83.3 (GND), U84.3 (GND), U85.3 (GND), U86.3 (GND), U87.3 (GND), U88.3 (GND), U89.3 (GND), U90.3 (GND), U91.3 (GND), U92.3 (GND), U93.3 (GND), U94.3 (GND), U95.3 (GND), U96.3 (GND), U97.3 (GND), U98.3 (GND), U99.3 (GND), U100.3 (GND), U101.3 (GND), U102.3 (GND), U103.3 (GND), U104.3 (GND), U105.3 (GND), U106.3 (GND), U107.3 (GND), U108.3 (GND), U109.3 (GND), U110.3 (GND), U111.3 (GND), U112.3 (GND), U113.3 (GND), U114.3 (GND), U115.3 (GND), U116.3 (GND), U117.3 (GND), U118.3 (GND), U119.3 (GND), U120.3 (GND), U121.3 (GND), U122.3 (GND), U123.3 (GND), U124.3 (GND), U125.3 (GND), U126.3 (GND), U127.3 (GND), U128.3 (GND), X1.9, X1.10
unnamed: U1.3 (OUT), U128.1 (Y)
unnamed: U2.3 (OUT), U127.1 (Y)
unnamed: U9.3 (OUT), U120.1 (Y)
unnamed: U3.3 (OUT), U126.1 (Y)
unnamed: U4.3 (OUT), U125.1 (Y)
unnamed: U5.3 (OUT), U124.1 (Y)
unnamed: U6.3 (OUT), U123.1 (Y)
unnamed: U7.3 (OUT), U122.1 (Y)
unnamed: U8.3 (OUT), U121.1 (Y)
unnamed: U10.3 (OUT), U119.1 (Y)
unnamed: U11.3 (OUT), U118.1 (Y)
unnamed: U12.3 (OUT), U117.1 (Y)
unnamed: U13.3 (OUT), U116.1 (Y)
unnamed: U14.3 (OUT), U115.1 (Y)
unnamed: U15.3 (OUT), U114.1 (Y)
unnamed: U16.3 (OUT), U113.1 (Y)
unnamed: U17.3 (OUT), U112.1 (Y)
unnamed: U18.3 (OUT), U111.1 (Y)
unnamed: U19.3 (OUT), U110.1 (Y)
unnamed: U20.3 (OUT), U109.1 (Y)
unnamed: U21.3 (OUT), U108.1 (Y)
unnamed: U22.3 (OUT), U107.1 (Y)
unnamed: U23.3 (OUT), U106.1 (Y)
unnamed: U24.3 (OUT), U105.1 (Y)
unnamed: U25.3 (OUT), U104.1 (Y)
unnamed: U26.3 (OUT), U103.1 (Y)
unnamed: U27.3 (OUT), U102.1 (Y)
unnamed: U28.3 (OUT), U101.1 (Y)
unnamed: U29.3 (OUT), U100.1 (Y)
unnamed: U30.3 (OUT), U99.1 (Y)
unnamed: U31.3 (OUT), U98.1 (Y)
unnamed: U32.3 (OUT), U97.1 (Y)
unnamed: U33.3 (OUT), U96.1 (Y)
unnamed: U34.3 (OUT), U95.1 (Y)
unnamed: U35.3 (OUT), U94.1 (Y)
unnamed: U36.3 (OUT), U93.1 (Y)
unnamed: U37.3 (OUT), U92.1 (Y)
unnamed: U38.3 (OUT), U91.1 (Y)
unnamed: U39.3 (OUT), U90.1 (Y)
unnamed: U40.3 (OUT), U89.1 (Y)
unnamed: U41.3 (OUT), U88.1 (Y)
unnamed: U42.3 (OUT), U87.1 (Y)
unnamed: U43.3 (OUT), U86.1 (Y)
unnamed: U44.3 (OUT), U85.1 (Y)
unnamed: U45.3 (OUT), U84.1 (Y)
unnamed: U46.3 (OUT), U83.1 (Y)
unnamed: U47.3 (OUT), U82.1 (Y)
unnamed: U48.3 (OUT), U81.1 (Y)
unnamed: U49.3 (OUT), U80.1 (Y)
unnamed: U50.3 (OUT), U79.1 (Y)
unnamed: U51.3 (OUT), U78.1 (Y)
unnamed: U52.3 (OUT), U77.1 (Y)
unnamed: U53.3 (OUT), U76.1 (Y)
unnamed: U54.3 (OUT), U75.1 (Y)
unnamed: U55.3 (OUT), U74.1 (Y)
unnamed: U56.3 (OUT), U73.1 (Y)
unnamed: U57.3 (OUT), U72.1 (Y)
unnamed: U58.3 (OUT), U71.1 (Y)
unnamed: U59.3 (OUT), U70.1 (Y)
unnamed: U60.3 (OUT), U69.1 (Y)
unnamed: U61.3 (OUT), U68.1 (Y)
unnamed: U62.3 (OUT), U67.1 (Y)
unnamed: U63.3 (OUT), U66.1 (Y)
unnamed: U64.3 (OUT), U65.1 (Y)
ROW0: U121.2 (Z), U122.2 (Z), U123.2 (Z), U124.2 (Z), U125.2 (Z), U126.2 (Z), U127.2 (Z), U128.2 (Z), X1.1
ROW1: U113.2 (Z), U114.2 (Z), U115.2 (Z), U116.2 (Z), U117.2 (Z), U118.2 (Z), U119.2 (Z), U120.2 (Z), X1.2
ROW2: U105.2 (Z), U106.2 (Z), U107.2 (Z), U108.2 (Z), U109.2 (Z), U110.2 (Z), U111.2 (Z), U112.2 (Z), X1.3
ROW3: U97.2 (Z), U98.2 (Z), U99.2 (Z), U100.2 (Z), U101.2 (Z), U102.2 (Z), U103.2 (Z), U104.2 (Z), X1.4
ROW4: U89.2 (Z), U90.2 (Z), U91.2 (Z), U92.2 (Z), U93.2 (Z), U94.2 (Z), U95.2 (Z), U96.2 (Z), X1.5
ROW5: U81.2 (Z), U82.2 (Z), U83.2 (Z), U84.2 (Z), U85.2 (Z), U86.2 (Z), U87.2 (Z), U88.2 (Z), X1.6
ROW6: U73.2 (Z), U74.2 (Z), U75.2 (Z), U76.2 (Z), U77.2 (Z), U78.2 (Z), U79.2 (Z), U80.2 (Z), X1.7
ROW7: U65.2 (Z), U66.2 (Z), U67.2 (Z), U68.2 (Z), U69.2 (Z), U70.2 (Z), U71.2 (Z), U72.2 (Z), X1.8
VCC: C1.1, C2.1, C3.1, C4.1, C5.1, C6.1, C7.1, C8.1, C9.1, C10.1, C11.1, C12.1, C13.1, C14.1, C15.1, C16.1, C17.1, C18.1, C19.1, C20.1, C21.1, C22.1, C23.1, C24.1, C25.1, C26.1, C27.1, C28.1, C29.1, C30.1, C31.1, C32.1, C33.1, C34.1, C35.1, C36.1, C37.1, C38.1, C39.1, C40.1, C41.1, C42.1, C43.1, C44.1, C45.1, C46.1, C47.1, C48.1, C49.1, C50.1, C51.1, C52.1, C53.1, C54.1, C55.1, C56.1, U1.1 (VCC), U2.1 (VCC), U3.1 (VCC), U4.1 (VCC), U5.1 (VCC), U6.1 (VCC), U7.1 (VCC), U8.1 (VCC), U9.1 (VCC), U10.1 (VCC), U11.1 (VCC), U12.1 (VCC), U13.1 (VCC), U14.1 (VCC), U15.1 (VCC), U16.1 (VCC), U17.1 (VCC), U18.1 (VCC), U19.1 (VCC), U20.1 (VCC), U21.1 (VCC), U22.1 (VCC), U23.1 (VCC), U24.1 (VCC), U25.1 (VCC), U26.1 (VCC), U27.1 (VCC), U28.1 (VCC), U29.1 (VCC), U30.1 (VCC), U31.1 (VCC), U32.1 (VCC), U33.1 (VCC), U34.1 (VCC), U35.1 (VCC), U36.1 (VCC), U37.1 (VCC), U38.1 (VCC), U39.1 (VCC), U40.1 (VCC), U41.1 (VCC), U42.1 (VCC), U43.1 (VCC), U44.1 (VCC), U45.1 (VCC), U46.1 (VCC), U47.1 (VCC), U48.1 (VCC), U49.1 (VCC), U50.1 (VCC), U51.1 (VCC), U52.1 (VCC), U53.1 (VCC), U54.1 (VCC), U55.1 (VCC), U56.1 (VCC), U57.1 (VCC), U58.1 (VCC), U59.1 (VCC), U60.1 (VCC), U61.1 (VCC), U62.1 (VCC), U63.1 (VCC), U64.1 (VCC), U65.5 (VCC), U66.5 (VCC), U67.5 (VCC), U68.5 (VCC), U69.5 (VCC), U70.5 (VCC), U71.5 (VCC), U72.5 (VCC), U73.5 (VCC), U74.5 (VCC), U75.5 (VCC), U76.5 (VCC), U77.5 (VCC), U78.5 (VCC), U79.5 (VCC), U80.5 (VCC), U81.5 (VCC), U82.5 (VCC), U83.5 (VCC), U84.5 (VCC), U85.5 (VCC), U86.5 (VCC), U87.5 (VCC), U88.5 (VCC), U89.5 (VCC), U90.5 (VCC), U91.5 (VCC), U92.5 (VCC), U93.5 (VCC), U94.5 (VCC), U95.5 (VCC), U96.5 (VCC), U97.5 (VCC), U98.5 (VCC), U99.5 (VCC), U100.5 (VCC), U101.5 (VCC), U102.5 (VCC), U103.5 (VCC), U104.5 (VCC), U105.5 (VCC), U106.5 (VCC), U107.5 (VCC), U108.5 (VCC), U109.5 (VCC), U110.5 (VCC), U111.5 (VCC), U112.5 (VCC), U113.5 (VCC), U114.5 (VCC), U115.5 (VCC), U116.5 (VCC), U117.5 (VCC), U118.5 (VCC), U119.5 (VCC), U120.5 (VCC), U121.5 (VCC), U122.5 (VCC), U123.5 (VCC), U124.5 (VCC), U125.5 (VCC), U126.5 (VCC), U127.5 (VCC), U128.5 (VCC), X1.11, X1.12

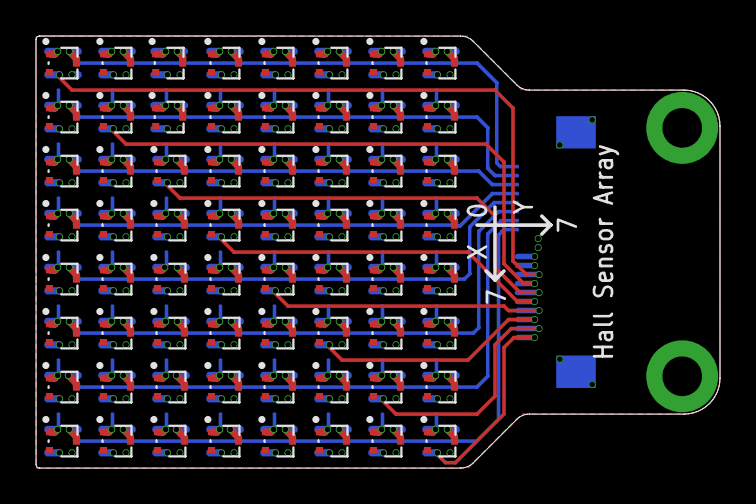
[picture p57: board Sensor_HallArray_StandAlone_2mm.brd from above]

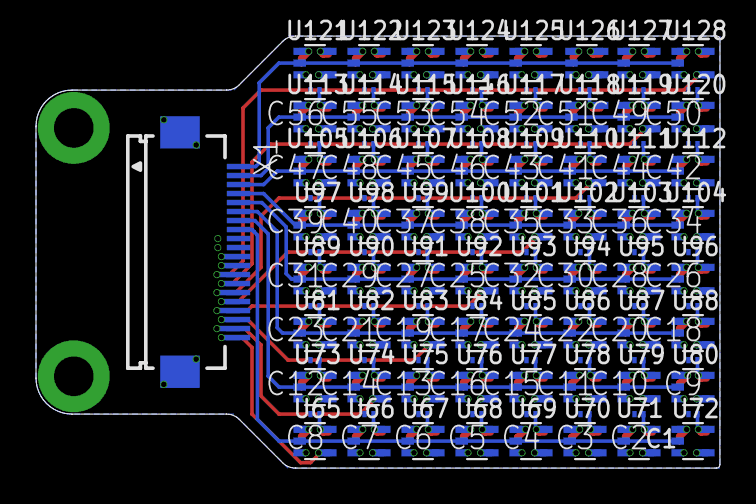
[picture p58: board Sensor_HallArray_StandAlone_2mm.brd from below]

Board: 4 copper layers, 38.0 x 24.0 mm, 185 parts (121 on the bottom side), 82 nets.
