stdlogicvector/modularCamera_hw/Sensor_Python.brd

## EAGLE design Sensor_Python.brd (2026-06-28)

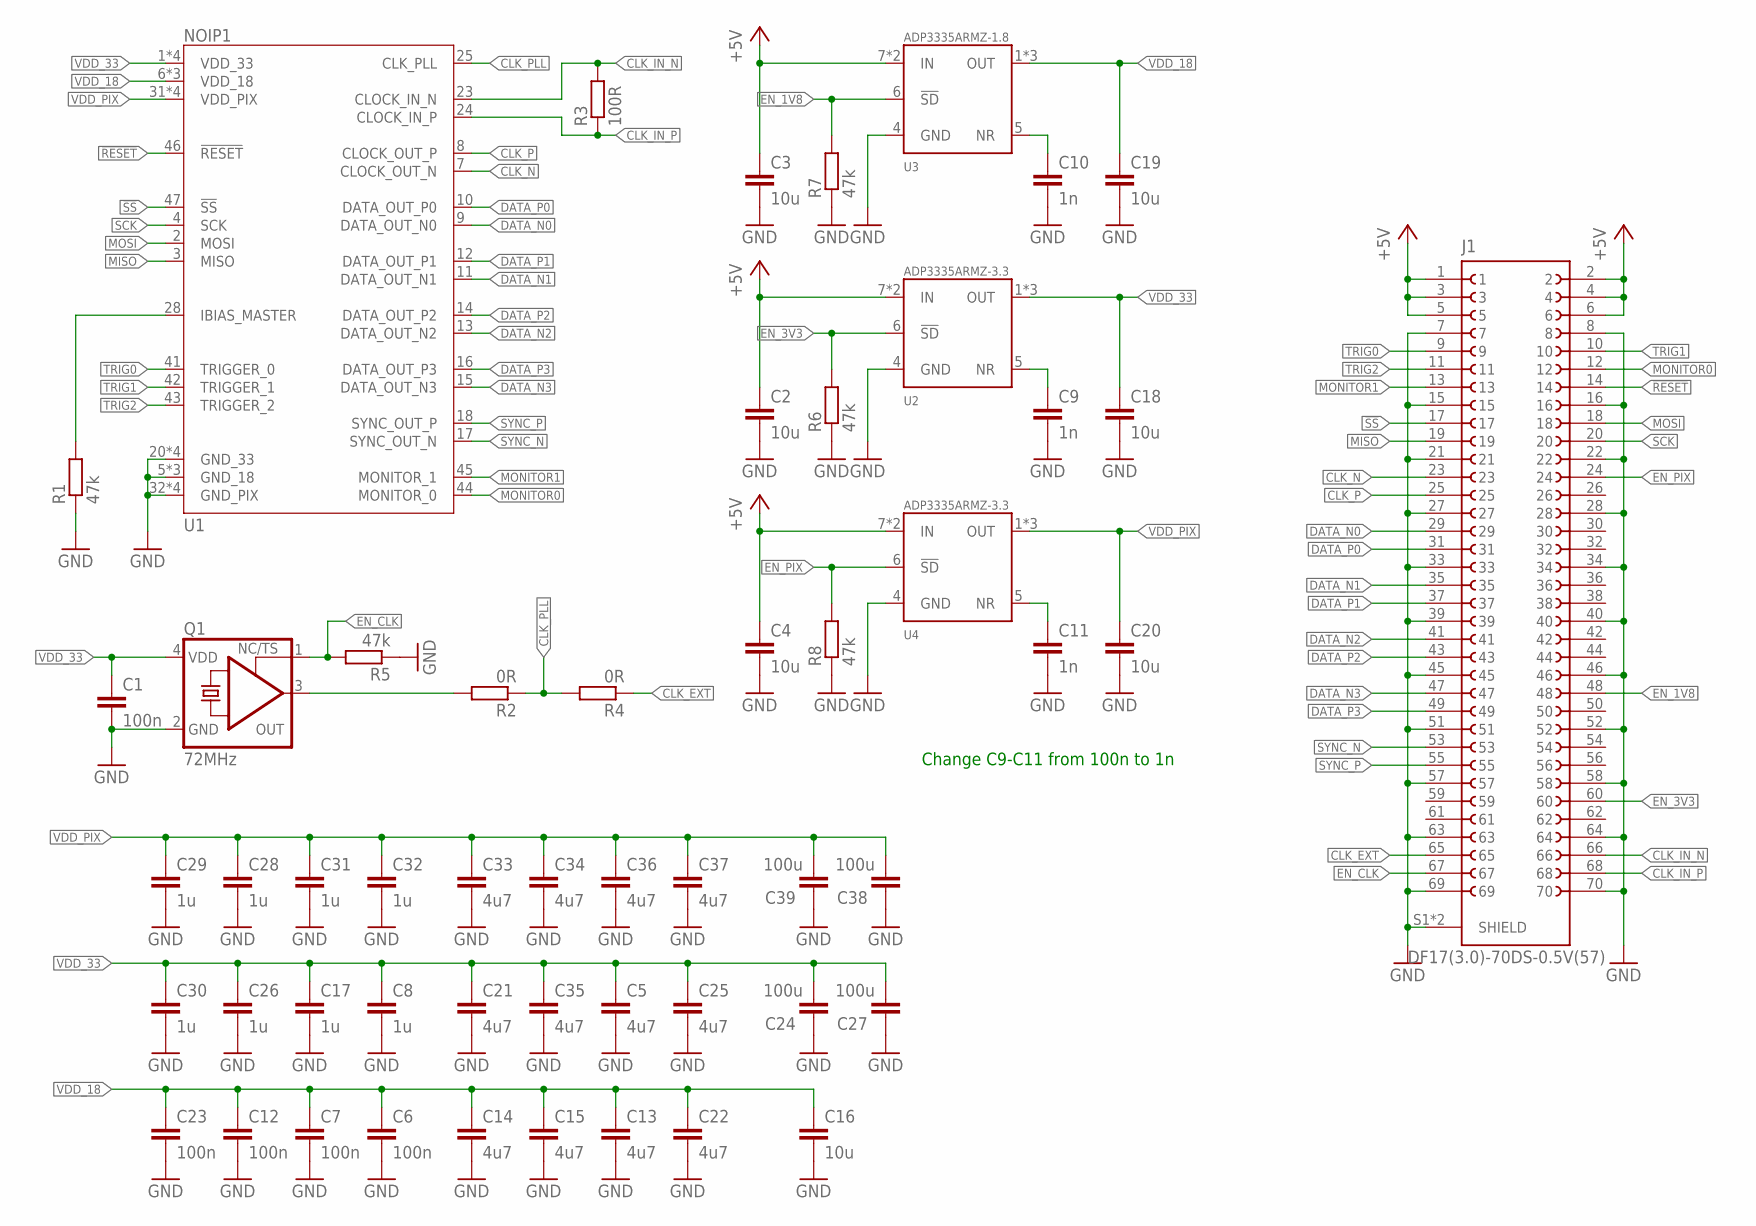
[picture p59: schematic Sensor_Python.sch]

Parts:
C1, C6, C7, C12, C23: 100n; C0402; LCSC C1525
C2, C3, C4, C16, C18, C19, C20: 10u; C0603
C5, C13, C14, C15, C21, C22, C25, C33, C34, C35, C36, C37: 4u7; C0603; LCSC C19666
C8, C17, C26, C28, C29, C30, C31, C32: 1u; C0402
C9, C10, C11: 1n; C0402; LCSC C1525
C24, C27, C38, C39: 100u; C1206; DIGIKEY 490-GRM31CD80J107MEA8LCT-ND
J1: DF17(3.0)-70DS-0.5V(57)
Q1: 72MHz; 3.2X2.5_KXO-V96; DIGIKEY 1473-SIT8208AC-23-33E-72.000000-ND
R1, R5, R6, R7, R8: 47k; R0402
R2, R4: 0R; R0402
R3: 100R; R0402
U1: NOIP1; LCC-44
U2, U4: ADP3335ARMZ-3.3; MSOP08; DIGIKEY 505-ADP3335ARMZ-3.3RL7CT-ND
U3: ADP3335ARMZ-1.8; MSOP08; DIGIKEY 505-ADP3335ARMZ-1.8-R7CT-ND

Connections:
!RESET: J1.14, U1.46 (!RESET)
!SS: J1.17, U1.47 (!SS)
+5V: C2.1, C3.1, C4.1, J1.1, J1.2, J1.3, J1.4, J1.5, J1.6, U2.7 (IN), U2.8 (IN), U3.7 (IN), U3.8 (IN), U4.7 (IN), U4.8 (IN)
CLK: Q1.3 (OUT), R2.2
CLK_EXT: J1.65, R4.1
CLK_IN_N: J1.66, R3.2, U1.23 (CLOCK_IN_N)
CLK_IN_P: J1.68, R3.1, U1.24 (CLOCK_IN_P)
CLK_N: J1.23, U1.7 (CLOCK_OUT_N)
CLK_P: J1.25, U1.8 (CLOCK_OUT_P)
CLK_PLL: R2.1, R4.2, U1.25 (CLK_PLL)
DATA_N0: J1.29, U1.9 (DATA_OUT_N0)
DATA_N1: J1.35, U1.11 (DATA_OUT_N1)
DATA_N2: J1.41, U1.13 (DATA_OUT_N2)
DATA_N3: J1.47, U1.15 (DATA_OUT_N3)
DATA_P0: J1.31, U1.10 (DATA_OUT_P0)
DATA_P1: J1.37, U1.12 (DATA_OUT_P1)
DATA_P2: J1.43, U1.14 (DATA_OUT_P2)
DATA_P3: J1.49, U1.16 (DATA_OUT_P3)
EN_1V8: J1.48, R7.2, U3.6 (!SD)
EN_3V3: J1.60, R6.2, U2.6 (!SD)
EN_CLK: J1.67, Q1.1 (TS), R5.2
EN_PIX: J1.24, R8.2, U4.6 (!SD)
GND: C1.2, C2.2, C3.2, C4.2, C5.2, C6.2, C7.2, C8.2, C9.2, C10.2, C11.2, C12.2, C13.2, C14.2, C15.2, C16.2, C17.2, C18.2, C19.2, C20.2, C21.2, C22.2, C23.2, C24.2, C25.2, C26.2, C27.2, C28.2, C29.2, C30.2, C31.2, C32.2, C33.2, C34.2, C35.2, C36.2, C37.2, C38.2, C39.2, J1.7, J1.8, J1.15, J1.16, J1.21, J1.22, J1.27, J1.28, J1.33, J1.34, J1.39, J1.40, J1.45, J1.46, J1.51, J1.52, J1.57, J1.58, J1.63, J1.64, J1.69, J1.70, J1.S1 (SHIELD), J1.S2 (SHIELD), Q1.2 (GND), R1.1, R5.1, R6.1, R7.1, R8.1, U1.5 (GND_18), U1.20 (GND_33), U1.21 (GND_18), U1.27 (GND_18), U1.30 (GND_33), U1.32 (GND_PIX), U1.34 (GND_PIX), U1.35 (GND_33), U1.37 (GND_PIX), U1.39 (GND_PIX), U1.48 (GND_33), U2.4 (GND), U3.4 (GND), U4.4 (GND)
MISO: J1.19, U1.3 (MISO)
MONITOR0: J1.12, U1.44 (MONITOR_0)
MONITOR1: J1.13, U1.45 (MONITOR_1)
MOSI: J1.18, U1.2 (MOSI)
unnamed: R1.2, U1.28 (IBIAS_MASTER)
unnamed: C11.1, U4.5 (NR)
unnamed: C10.1, U3.5 (NR)
unnamed: C9.1, U2.5 (NR)
SCK: J1.20, U1.4 (SCK)
SYNC_N: J1.53, U1.17 (SYNC_OUT_N)
SYNC_P: J1.55, U1.18 (SYNC_OUT_P)
TRIG0: J1.9, U1.41 (TRIGGER_0)
TRIG1: J1.10, U1.42 (TRIGGER_1)
TRIG2: J1.11, U1.43 (TRIGGER_2)
VDD_18: C6.1, C7.1, C12.1, C13.1, C14.1, C15.1, C16.1, C19.1, C22.1, C23.1, U1.6 (VDD_18), U1.22 (VDD_18), U1.26 (VDD_18), U3.1 (OUT), U3.2 (OUT), U3.3 (OUT)
VDD_33: C1.1, C5.1, C8.1, C17.1, C18.1, C21.1, C24.1, C25.1, C26.1, C27.1, C30.1, C35.1, Q1.4 (VDD), U1.1 (VDD_33), U1.19 (VDD_33), U1.29 (VDD_33), U1.36 (VDD_33), U2.1 (OUT), U2.2 (OUT), U2.3 (OUT)
VDD_PIX: C20.1, C28.1, C29.1, C31.1, C32.1, C33.1, C34.1, C36.1, C37.1, C38.1, C39.1, U1.31 (VDD_PIX), U1.33 (VDD_PIX), U1.38 (VDD_PIX), U1.40 (VDD_PIX), U4.1 (OUT), U4.2 (OUT), U4.3 (OUT)

Notes on the sheet:
Change C9-C11 from 100n to 1n

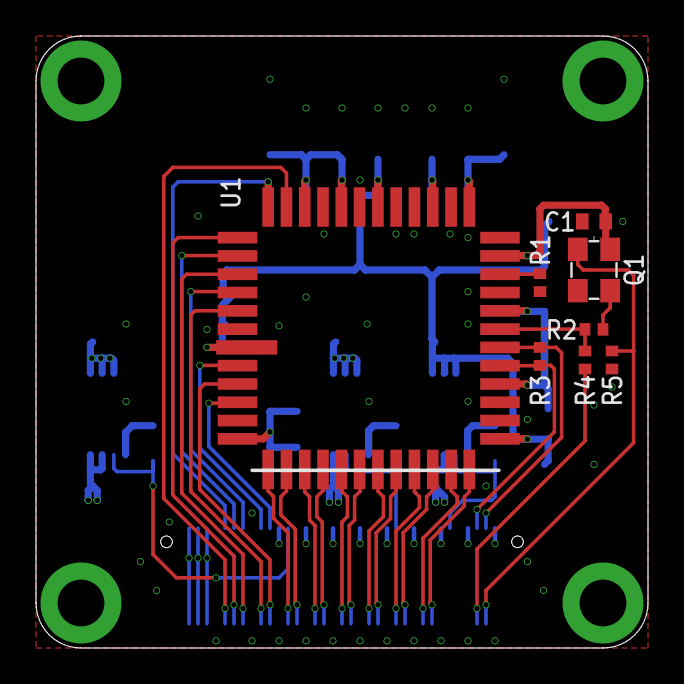
[picture p60: board Sensor_Python.brd from above]

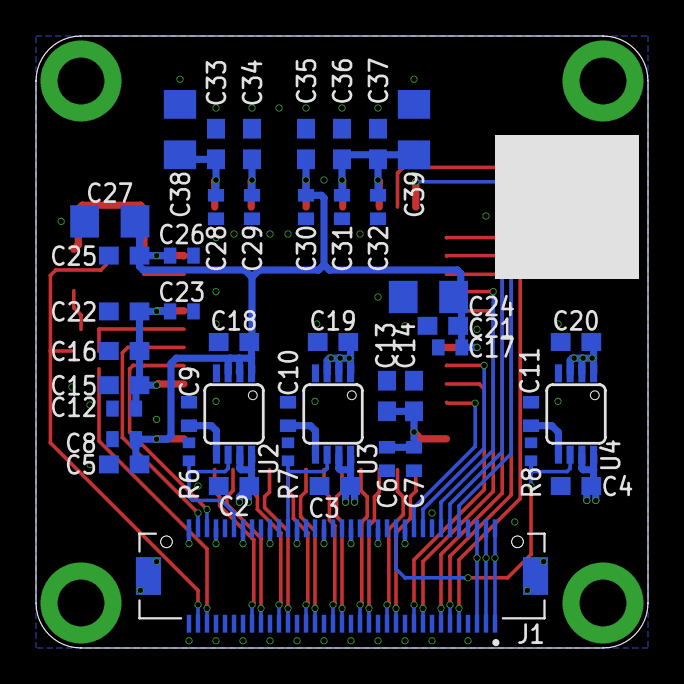
[picture p61: board Sensor_Python.brd from below]

Board: 4 copper layers, 34.0 x 34.0 mm, 53 parts (45 on the bottom side), 40 nets.
