stdlogicvector/modularCamera_hw/Sensor_LinearCCD_Socket.brd

## EAGLE design Sensor_LinearCCD_Socket.brd (2026-06-28)

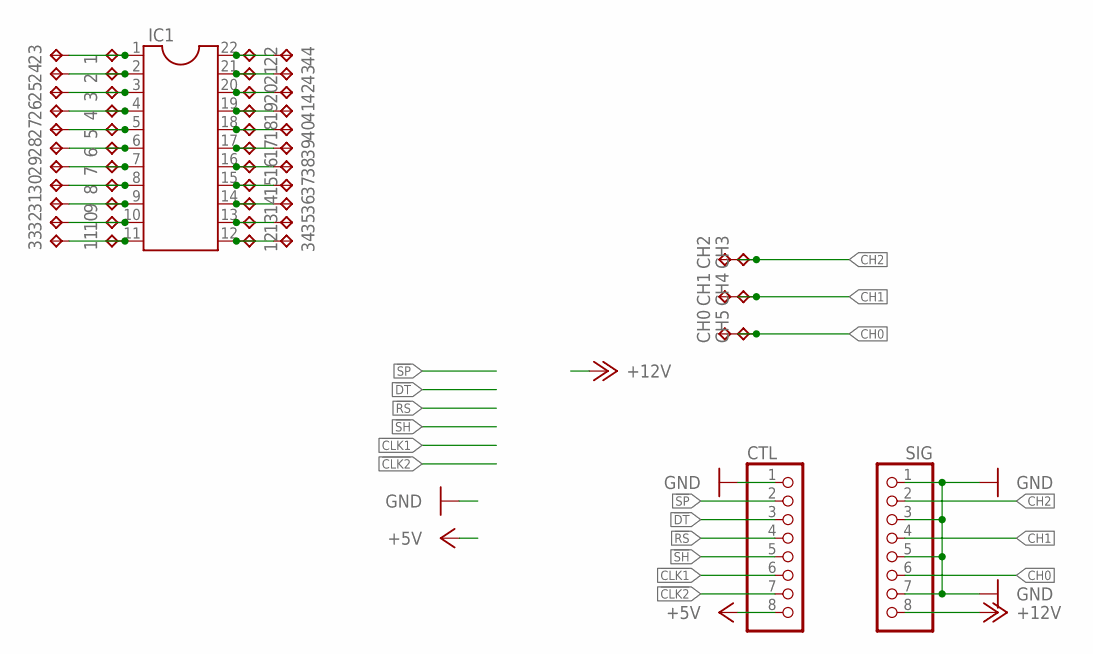
[picture p62: schematic Sensor_LinearCCD_Socket.sch]

Parts:
1, 2, 3, 4, 5, 6, 7, 8, 9, 10, 11, 12, 13, 14, 15, 16, 17, 18, 19, 20, 21, 22, 23, 24, 25, 26, 27, 28, 29, 30, 31, 32, 33, 34, 35, 36, 37, 38, 39, 40, 41, 42, 43, 44: TPTP15SQ; TP15SQ
CH0, CH1, CH2, CH3, CH4, CH5: TPTP15SQ; TP15SQ
CTL: PINHD-1X8_2.00; 1X08M
IC1: DIL22-4
SIG: PINHD-1X8_2.00; 1X08M

Connections:
!CLK1!: CTL.6
!CLK2!: CTL.7
!DT!: CTL.3
!RS!: CTL.4
!SH!: CTL.5
!SP!: CTL.2
+5V: CTL.8
+12V: SIG.8
CH0: CH0.TP, CH5.TP, SIG.6
CH1: CH1.TP, CH4.TP, SIG.4
CH2: CH2.TP, CH3.TP, SIG.2
GND: CTL.1, SIG.1, SIG.3, SIG.5, SIG.7
unnamed: 1.TP, 23.TP, IC1.1
unnamed: 2.TP, 24.TP, IC1.2
unnamed: 3.TP, 25.TP, IC1.3
unnamed: 4.TP, 26.TP, IC1.4
unnamed: 5.TP, 27.TP, IC1.5
unnamed: 6.TP, 28.TP, IC1.6
unnamed: 7.TP, 29.TP, IC1.7
unnamed: 8.TP, 30.TP, IC1.8
unnamed: 9.TP, 31.TP, IC1.9
unnamed: 10.TP, 32.TP, IC1.10
unnamed: 11.TP, 33.TP, IC1.11
unnamed: 12.TP, 34.TP, IC1.12
unnamed: 13.TP, 35.TP, IC1.13
unnamed: 14.TP, 36.TP, IC1.14
unnamed: 15.TP, 37.TP, IC1.15
unnamed: 16.TP, 38.TP, IC1.16
unnamed: 17.TP, 39.TP, IC1.17
unnamed: 18.TP, 40.TP, IC1.18
unnamed: 19.TP, 41.TP, IC1.19
unnamed: 20.TP, 42.TP, IC1.20
unnamed: 21.TP, 43.TP, IC1.21
unnamed: 22.TP, 44.TP, IC1.22

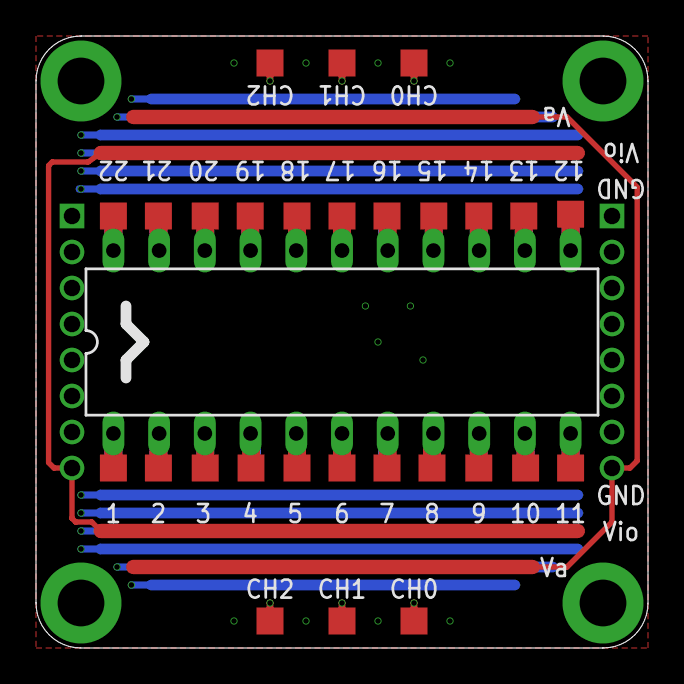
[picture p63: board Sensor_LinearCCD_Socket.brd from above]

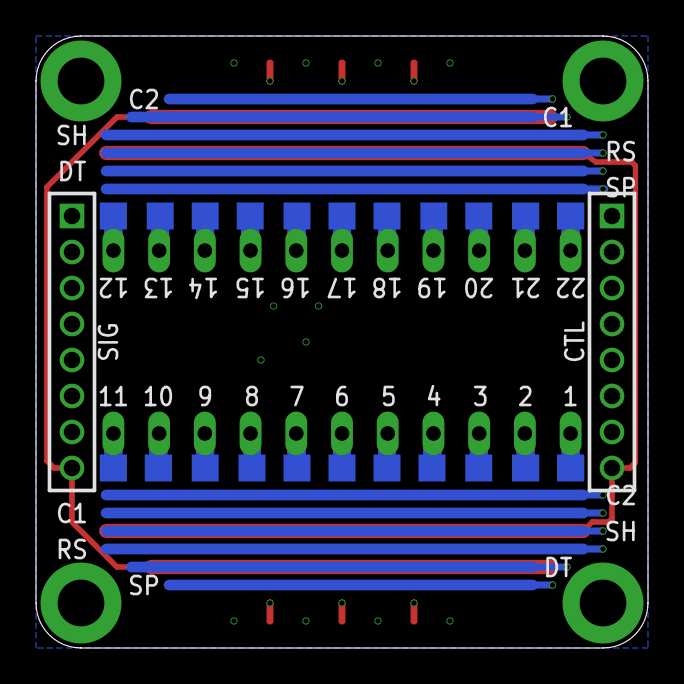
[picture p64: board Sensor_LinearCCD_Socket.brd from below]

Board: 4 copper layers, 34.0 x 34.0 mm, 53 parts (24 on the bottom side), 26 nets.
