stdlogicvector/modularCamera_hw/Sensor_LinearCCD.brd

## EAGLE design Sensor_LinearCCD.brd (2026-06-28)

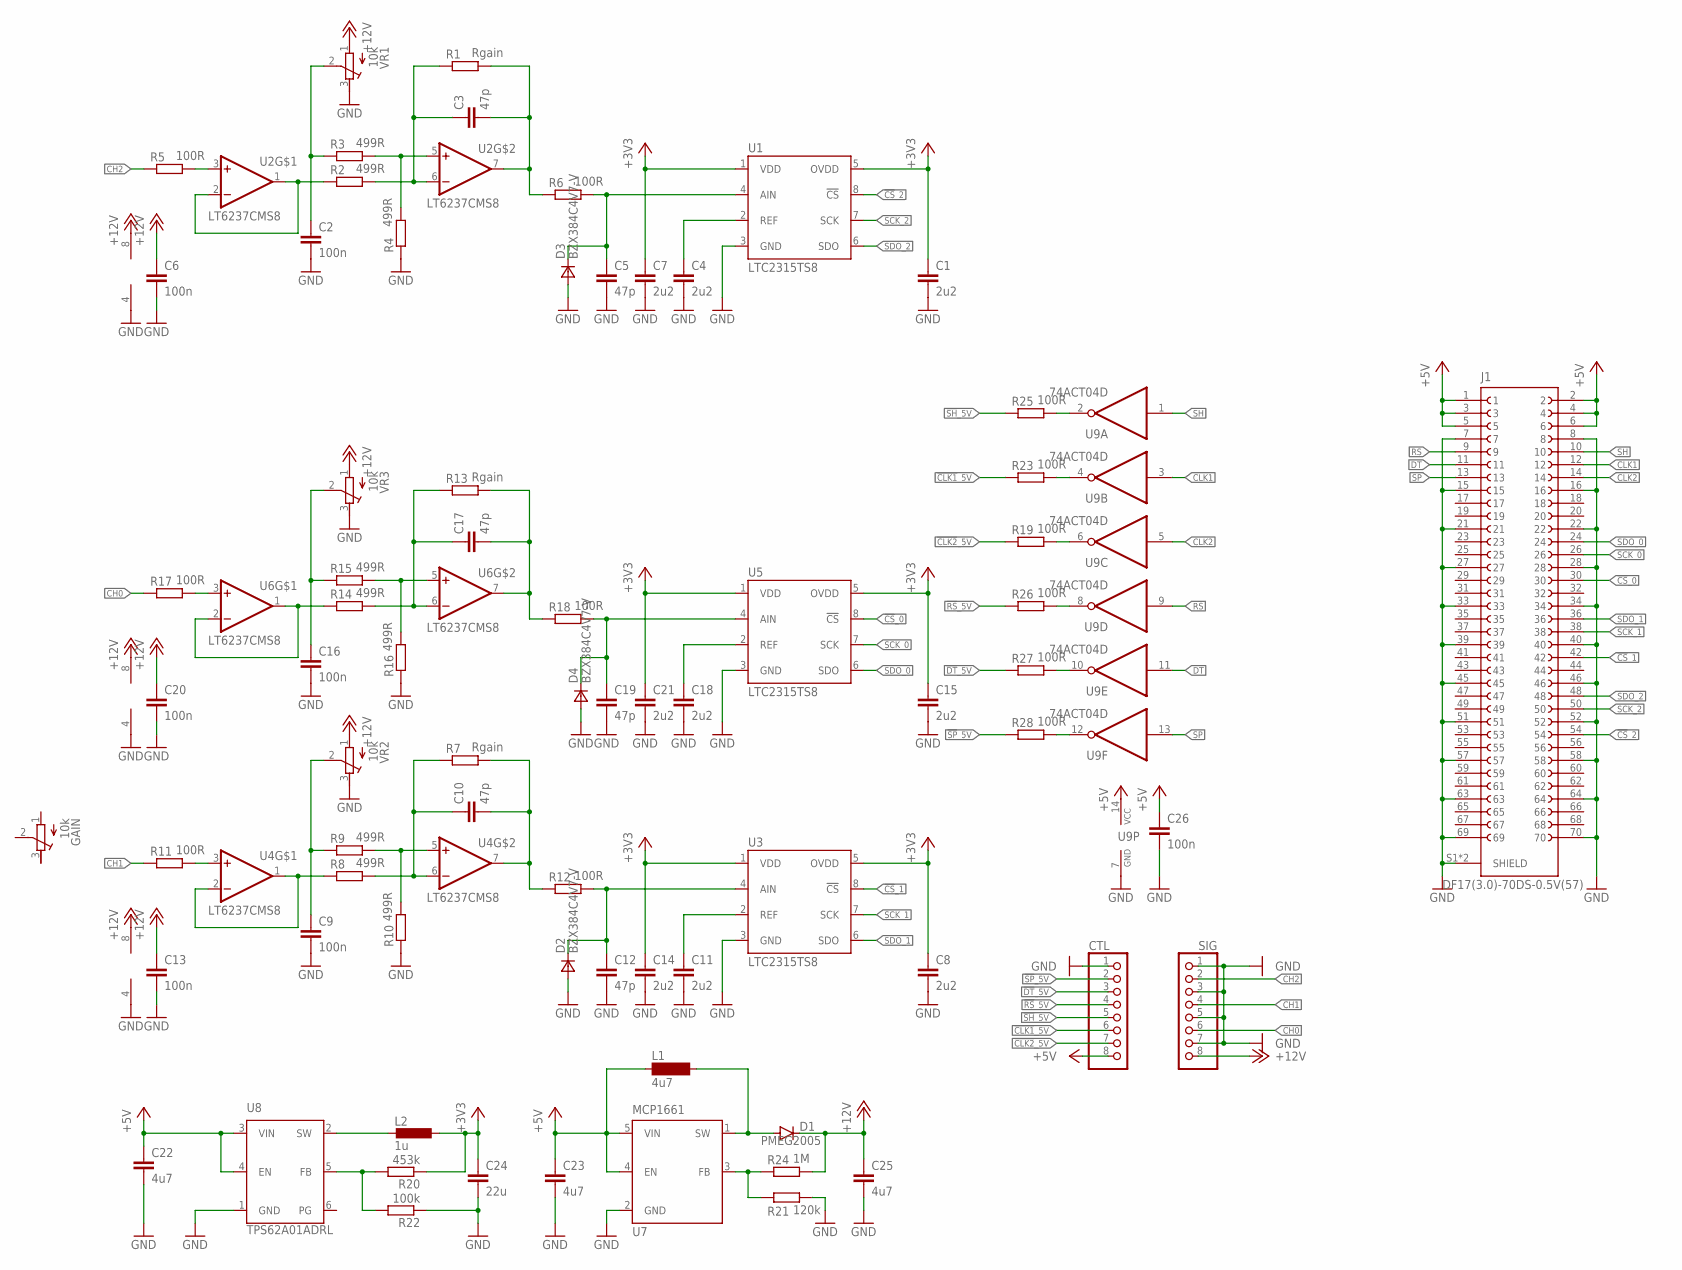
[picture p65: schematic Sensor_LinearCCD.sch]

Parts:
C1, C4, C7, C8, C11, C14, C15, C18, C21: 2u2; C0603; LCSC C19666
C2, C6, C9, C13, C16, C20, C26: 100n; C0402
C3, C5, C10, C12, C17, C19: 47p; C0402
C22, C23, C25: 4u7; C0603; LCSC C19666
C24: 22u; C0603; LCSC C109448
CTL: PINHD-1X8_2.00; 1X08M
D1: PMEG2005; SOD123; DIGIKEY 1727-7330-1-ND
D2, D3, D4: BZX384C4V7-V; SOD323
GAIN: 10k; RTRIM3224J
J1: DF17(3.0)-70DS-0.5V(57)
L1: 4u7; L4012
L2: 1u; L1008; MPN LQM2HPN1R0MG0L; DIGIKEY 490-5112-1-ND
R1, R7, R13: Rgain; R0402
R2, R3, R4, R8, R9, R10, R14, R15, R16: 499R; R0402
R5, R6, R11, R12, R17, R18, R19, R23, R25, R26, R27, R28: 100R; R0402
R20: 453k; R0402; LCSC C137978
R21: 120k; R0402
R22: 100k; R0402; DIGIKEY RMCF0402FT100KCT-ND
R24: 1M; R0402
SIG: PINHD-1X8_2.00; 1X08M
U1, U3, U5: LTC2315TS8; SOT23-8L
U2, U4, U6: LT6237CMS8; MSOP08
U7: MCP1661; SOT23-5L; DIGIKEY MCP1661T-E/OTCT-ND
U8: TPS62A01ADRL; SOTFL50P160X60-6N; DIGIKEY 296-TPS62A01ADRLRCT-ND
U9: 74ACT04D; SO14
VR1, VR2, VR3: 10k; RTRIM3224J

Connections:
!CLK1!_5V: CTL.6, R23.1
!CLK2!_5V: CTL.7, R19.1
!CS!_0: J1.30, U5.8 (!CS)
!CS!_1: J1.42, U3.8 (!CS)
!CS!_2: J1.54, U1.8 (!CS)
!DT!_5V: CTL.3, R27.1
!RS!_5V: CTL.4, R26.1
!SH!_5V: CTL.5, R25.1
!SP!_5V: CTL.2, R28.1
+3V3: C1.1, C7.1, C8.1, C14.1, C15.1, C21.1, C24.1, L2.1, R20.1, U1.1 (VDD), U1.5 (OVDD), U3.1 (VDD), U3.5 (OVDD), U5.1 (VDD), U5.5 (OVDD)
+5V: C22.1, C23.1, C26.1, CTL.8, J1.1, J1.2, J1.3, J1.4, J1.5, J1.6, L1.1, U7.4 (EN), U7.5 (VIN), U8.3 (VIN), U8.4 (EN), U9.14 (VCC)
+12V: C6.1, C13.1, C20.1, C25.1, D1.C, R24.2, SIG.8, U2.8 (V+), U4.8 (V+), U6.8 (V+), VR1.1 (A), VR2.1 (A), VR3.1 (A)
CH0: R17.1, SIG.6
CH1: R11.1, SIG.4
CH2: R5.1, SIG.2
CLK1: J1.12, U9.3 (I)
CLK2: J1.14, U9.5 (I)
DT: J1.11, U9.11 (I)
GND: C1.2, C2.2, C4.2, C5.2, C6.2, C7.2, C8.2, C9.2, C11.2, C12.2, C13.2, C14.2, C15.2, C16.2, C18.2, C19.2, C20.2, C21.2, C22.2, C23.2, C24.2, C25.2, C26.2, CTL.1, D2.2 (A), D3.2 (A), D4.2 (A), J1.7, J1.8, J1.15, J1.16, J1.21, J1.22, J1.27, J1.28, J1.33, J1.34, J1.39, J1.40, J1.45, J1.46, J1.51, J1.52, J1.57, J1.58, J1.63, J1.64, J1.69, J1.70, J1.S1 (SHIELD), J1.S2 (SHIELD), R4.1, R10.1, R16.1, R21.2, R22.1, SIG.1, SIG.3, SIG.5, SIG.7, U1.3 (GND), U2.4 (V-), U3.3 (GND), U4.4 (V-), U5.3 (GND), U6.4 (V-), U7.2 (GND), U8.1 (GND), U9.7 (GND), VR1.3 (E), VR2.3 (E), VR3.3 (E)
unnamed: R21.1, R24.1, U7.3 (FB)
unnamed: C11.1, U3.2 (REF)
unnamed: D1.A, L1.2, U7.1 (SW)
unnamed: C12.1, D2.1 (C), R12.2, U3.4 (AIN)
unnamed: R8.1, U4.1 (OUT), U4.2 (-IN)
unnamed: R11.2, U4.3 (+IN)
unnamed: C10.1, R7.1, R8.2, U4.6 (-IN)
unnamed: C10.2, R7.2, R12.1, U4.7 (OUT)
unnamed: R25.2, U9.2 (O)
unnamed: R23.2, U9.4 (O)
unnamed: R19.2, U9.6 (O)
unnamed: R26.2, U9.8 (O)
unnamed: R27.2, U9.10 (O)
unnamed: R28.2, U9.12 (O)
unnamed: C9.1, R9.1, VR2.2 (S)
unnamed: R9.2, R10.2, U4.5 (+IN)
unnamed: C18.1, U5.2 (REF)
unnamed: C19.1, D4.1 (C), R18.2, U5.4 (AIN)
unnamed: R14.1, U6.1 (OUT), U6.2 (-IN)
unnamed: R17.2, U6.3 (+IN)
unnamed: C17.1, R13.1, R14.2, U6.6 (-IN)
unnamed: C17.2, R13.2, R18.1, U6.7 (OUT)
unnamed: C16.1, R15.1, VR3.2 (S)
unnamed: R15.2, R16.2, U6.5 (+IN)
unnamed: C4.1, U1.2 (REF)
unnamed: C5.1, D3.1 (C), R6.2, U1.4 (AIN)
unnamed: R2.1, U2.1 (OUT), U2.2 (-IN)
unnamed: R5.2, U2.3 (+IN)
unnamed: C3.1, R1.1, R2.2, U2.6 (-IN)
unnamed: C3.2, R1.2, R6.1, U2.7 (OUT)
unnamed: C2.1, R3.1, VR1.2 (S)
unnamed: R3.2, R4.2, U2.5 (+IN)
unnamed: R20.2, R22.2, U8.5 (FB)
unnamed: L2.2, U8.2 (SW)
RS: J1.9, U9.9 (I)
SCK_0: J1.26, U5.7 (SCK)
SCK_1: J1.38, U3.7 (SCK)
SCK_2: J1.50, U1.7 (SCK)
SDO_0: J1.24, U5.6 (SDO)
SDO_1: J1.36, U3.6 (SDO)
SDO_2: J1.48, U1.6 (SDO)
SH: J1.10, U9.1 (I)
SP: J1.13, U9.13 (I)

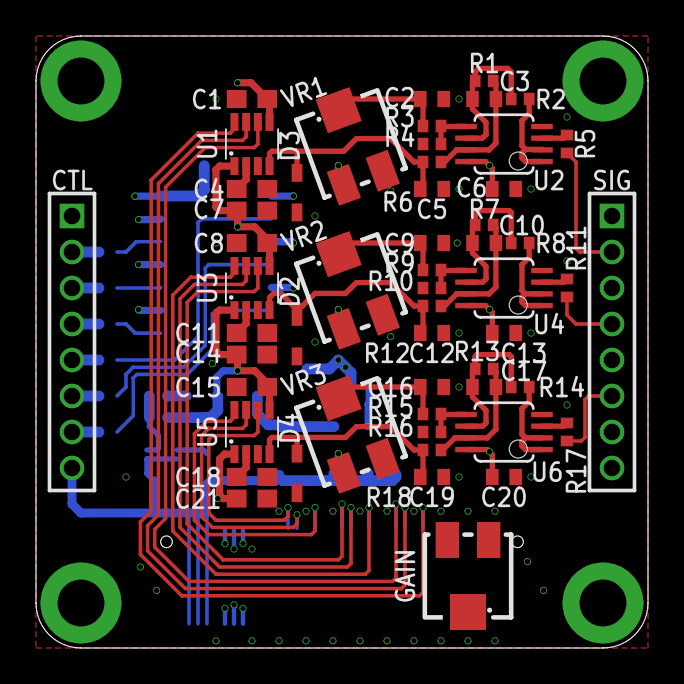
[picture p66: board Sensor_LinearCCD.brd from above]

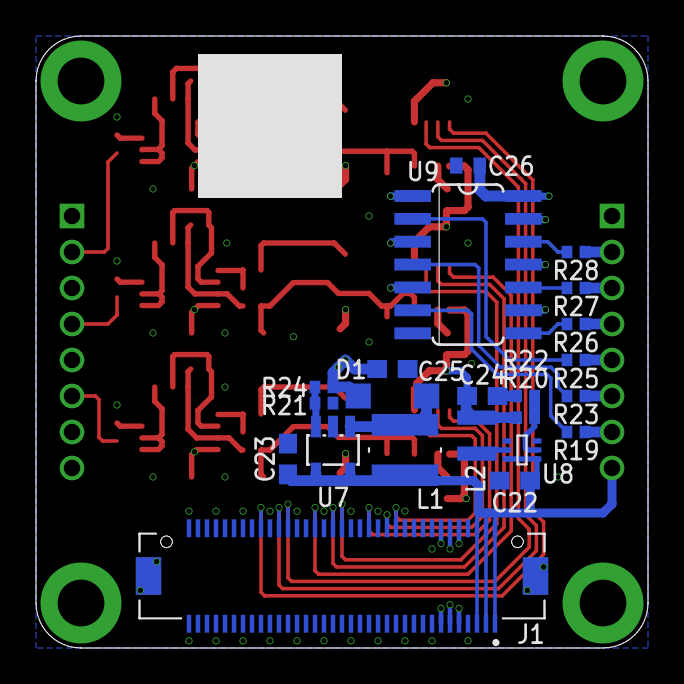
[picture p67: board Sensor_LinearCCD.brd from below]

Board: 4 copper layers, 34.0 x 34.0 mm, 76 parts (22 on the bottom side), 62 nets.
