stdlogicvector/modularCamera_hw/Interface_ETH.brd

## EAGLE design Interface_ETH.brd (2026-06-28)

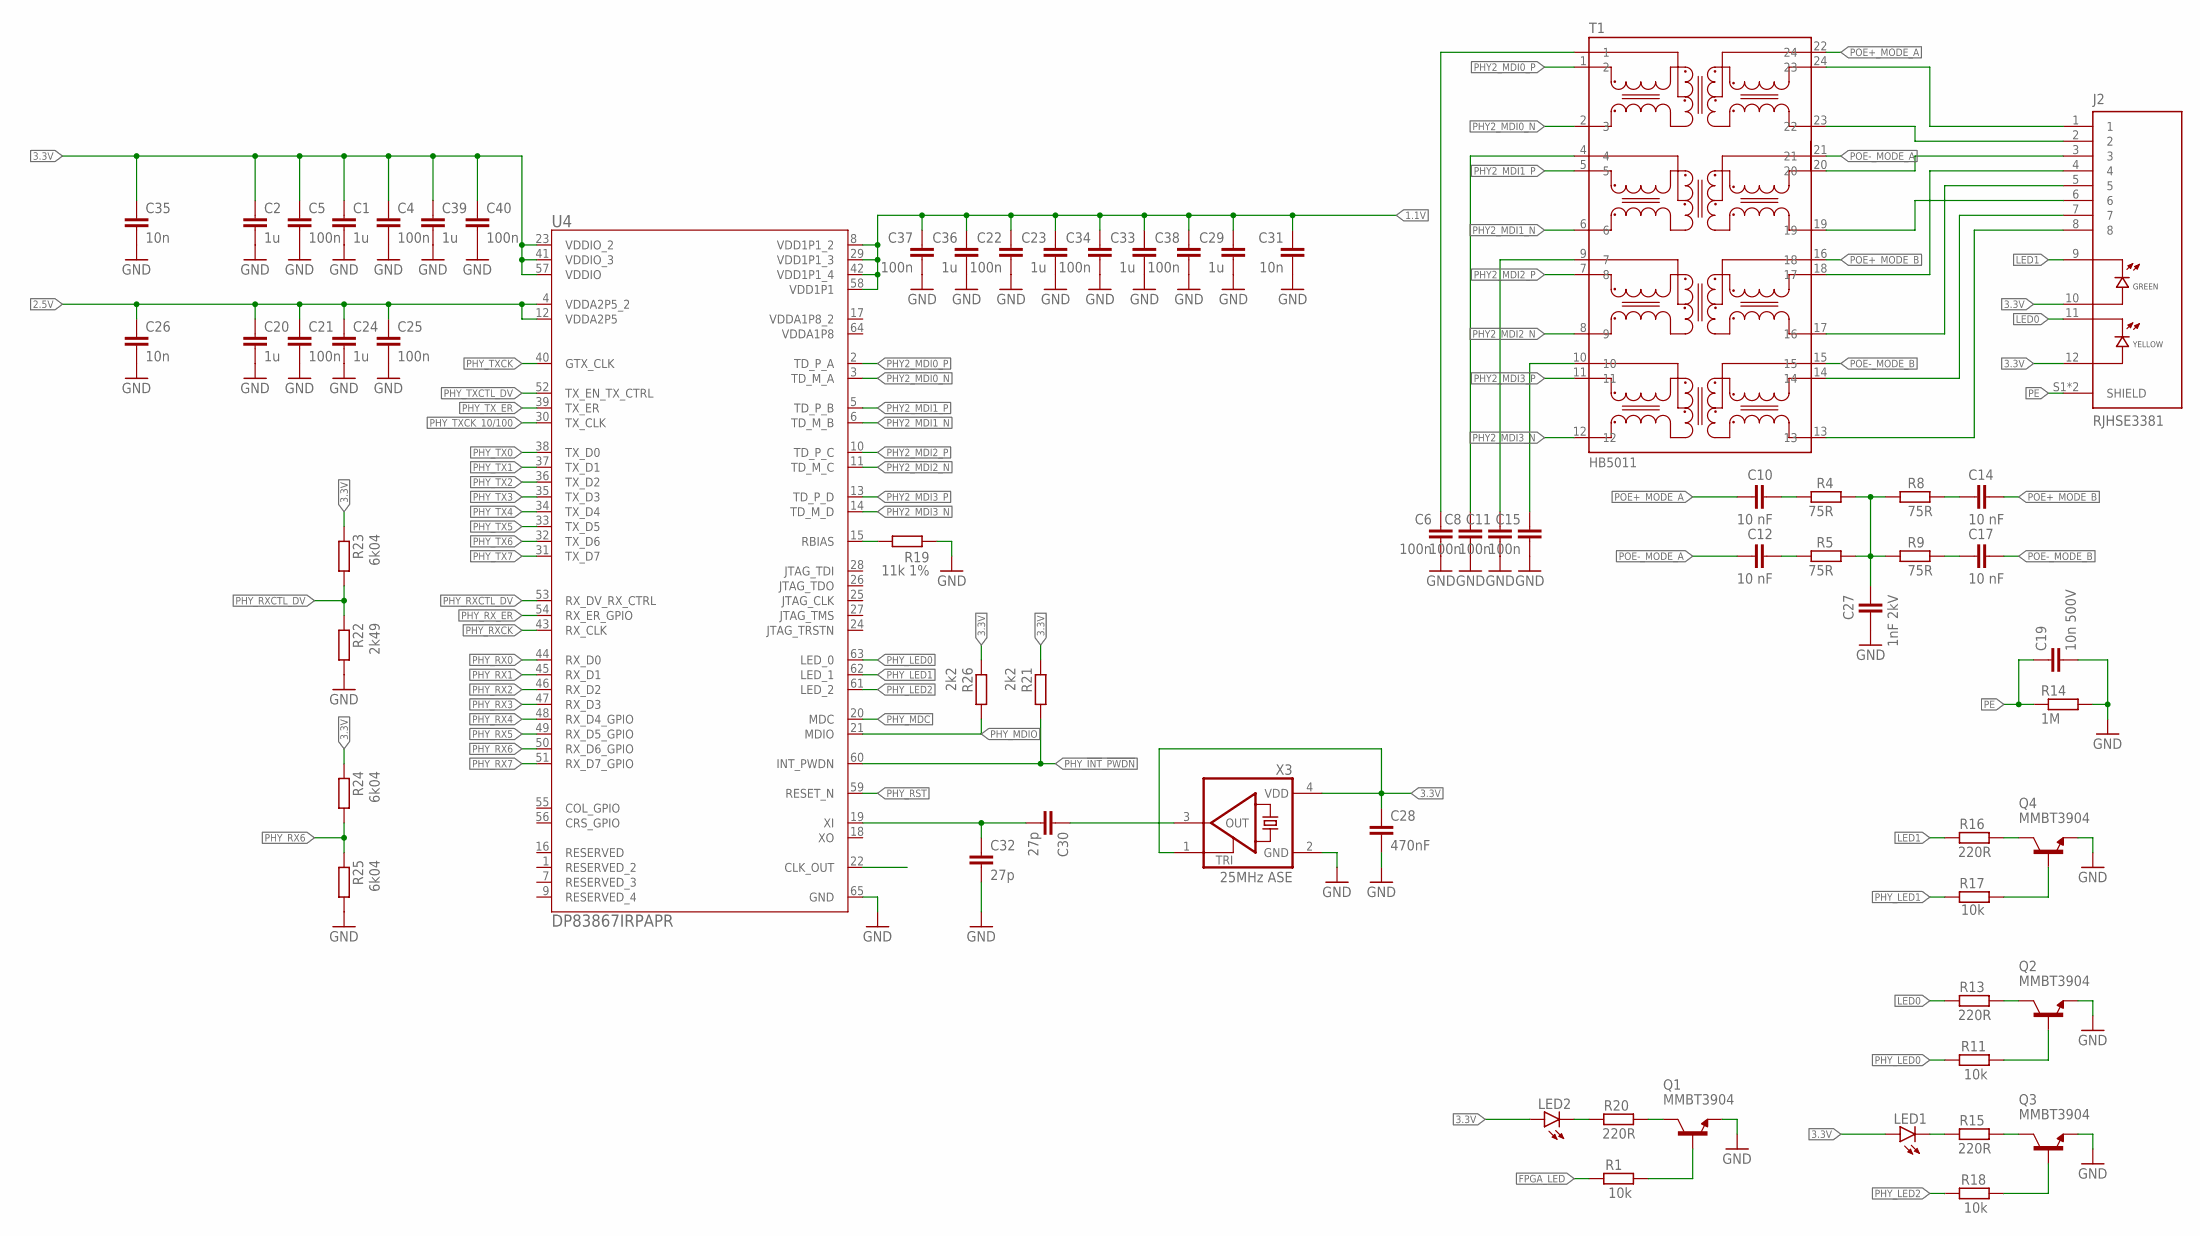
[picture p68: schematic Interface_ETH.sch, sheet 1, Ethernet]

Parts:
C1, C2, C20, C23, C24, C29, C33, C36, C39: 1u; C0402; FARNELL 2409032
C4, C5, C6, C8, C11, C15, C21, C22, C25, C34, C37, C38, C40: 100n; C0402; FARNELL 2409032
C10, C12, C14, C17: 10 nF; C0603; FARNELL 1288254
C19: 10n 500V; C0805
C26, C31, C35: 10n; C0402; FARNELL 2409032
C27: 1nF 2kV; C1206; FARNELL 1650716
C28: 470nF; C0402; FARNELL 2409032
C30, C32: 27p; C0402; FARNELL 2409032
J2: RJHSE3381; AMPHENOL_RJHSE3381; DIGIKEY 664-RJHSE3381-ND
LED1: LEDCHIP-LED0805; CHIP-LED0805
LED2: LEDCHIP-LED0603; CHIP-LED0603
Q1, Q2, Q3, Q4: MMBT3904; SOT23; FARNELL 1757935
R1, R11, R17, R18: 10k; R0603
R4, R5, R8, R9: 75R; R0603; FARNELL 1527343
R13, R15, R16, R20: 220R; R0603
R14: 1M; R0603
R19: 11k 1%; R0402; FARNELL 1652885
R21, R26: 2k2; R0402; FARNELL 1652885
R22: 2k49; R0402; FARNELL 1652885
R23, R24, R25: 6k04; R0402; FARNELL 1652885
T1: HB5011; DIGIKEY 931-TM82467NLCT-ND
U4: DP83867IRPAPR; PAP0064M_N
X3: 25MHz ASE; ASE; DIGIKEY 535-9577-1-ND

Connections:
1.1V: C22.1, C23.1, C29.1, C31.1, C33.1, C34.1, C36.1, C37.1, C38.1, U4.8 (VDD1P1_2), U4.29 (VDD1P1_3), U4.42 (VDD1P1_4), U4.58 (VDD1P1); also elsewhere on the board
2.5V: C20.1, C21.1, C24.1, C25.1, C26.1, U4.4 (VDDA2P5_2), U4.12 (VDDA2P5); also elsewhere on the board
3.3V: C1.1, C2.1, C4.1, C5.1, C28.1, C35.1, C39.1, C40.1, J2.10, J2.12, LED1.A, LED2.A, R21.1, R23.1, R24.1, R26.1, U4.23 (VDDIO_2), U4.41 (VDDIO_3), U4.57 (VDDIO), X3.1 (TRI), X3.4 (VDD); also elsewhere on the board
ETH_1: J2.1, T1.24 (23)
ETH_2: J2.2, T1.23 (22)
ETH_3: J2.3, T1.20
ETH_4: J2.4, T1.18 (17)
ETH_5: J2.5, T1.17 (16)
ETH_6: J2.6, T1.19
ETH_7: J2.7, T1.14
ETH_8: J2.8, T1.13
FPGA_LED: R1.1; also elsewhere on the board
GND: C1.2, C2.2, C4.2, C5.2, C6.2, C8.2, C11.2, C15.2, C19.2, C20.2, C21.2, C22.2, C23.2, C24.2, C25.2, C26.2, C27.2, C28.2, C29.2, C31.2, C32.2, C33.2, C34.2, C35.2, C36.2, C37.2, C38.2, C39.2, C40.2, Q1.2 (E), Q2.2 (E), Q3.2 (E), Q4.2 (E), R14.2, R19.1, R22.2, R25.2, U4.65 (GND), X3.2 (GND); also elsewhere on the board
LED0: J2.11, R13.1
LED1: J2.9, R16.1
unnamed: C30.1, X3.3 (OUT)
unnamed: Q3.3 (C), R15.2
unnamed: Q3.1 (B), R18.2
unnamed: C15.1, T1.10
unnamed: C11.1, T1.9 (7)
unnamed: C8.1, T1.4
unnamed: C6.1, T1.3 (1)
unnamed: C30.2, C32.1, U4.19 (XI)
unnamed: Q1.3 (C), R20.2
unnamed: LED1.C, R15.1
unnamed: Q1.1 (B), R1.2
unnamed: LED2.C, R20.1
unnamed: C14.1, R8.2
unnamed: C17.1, R9.2
unnamed: C10.1, R4.2
unnamed: C12.1, R5.2
unnamed: C27.1, R4.1, R5.1, R8.1, R9.1
unnamed: R19.2, U4.15 (RBIAS)
unnamed: Q4.3 (C), R16.2
unnamed: Q2.3 (C), R13.2
unnamed: Q4.1 (B), R17.2
unnamed: Q2.1 (B), R11.2
PE: C19.1, J2.S1 (SHIELD), J2.S2 (SHIELD), R14.1; also elsewhere on the board
PHY2_MDI0_N: T1.2 (3), U4.3 (TD_M_A)
PHY2_MDI0_P: T1.1 (2), U4.2 (TD_P_A)
PHY2_MDI1_N: T1.6, U4.6 (TD_M_B)
PHY2_MDI1_P: T1.5, U4.5 (TD_P_B)
PHY2_MDI2_N: T1.8 (9), U4.11 (TD_M_C)
PHY2_MDI2_P: T1.7 (8), U4.10 (TD_P_C)
PHY2_MDI3_N: T1.12, U4.14 (TD_M_D)
PHY2_MDI3_P: T1.11, U4.13 (TD_P_D)
PHY_!INT!_!PWDN: R21.2, U4.60 (INT_PWDN); also elsewhere on the board
PHY_LED0: R11.1, U4.63 (LED_0)
PHY_LED1: R17.1, U4.62 (LED_1)
PHY_LED2: R18.1, U4.61 (LED_2)
PHY_MDC: U4.20 (MDC); also elsewhere on the board
PHY_MDIO: R26.2, U4.21 (MDIO); also elsewhere on the board
PHY_RST: U4.59 (RESET_N); also elsewhere on the board
PHY_RX0: U4.44 (RX_D0); also elsewhere on the board
PHY_RX1: U4.45 (RX_D1); also elsewhere on the board
PHY_RX2: U4.46 (RX_D2); also elsewhere on the board
PHY_RX3: U4.47 (RX_D3); also elsewhere on the board
PHY_RX4: U4.48 (RX_D4_GPIO); also elsewhere on the board
PHY_RX5: U4.49 (RX_D5_GPIO); also elsewhere on the board
PHY_RX6: R24.2, R25.1, U4.50 (RX_D6_GPIO); also elsewhere on the board
PHY_RX7: U4.51 (RX_D7_GPIO); also elsewhere on the board
PHY_RXCK: U4.43 (RX_CLK); also elsewhere on the board
PHY_RXCTL_DV: R22.1, R23.2, U4.53 (RX_DV_RX_CTRL); also elsewhere on the board
PHY_RX_ER: U4.54 (RX_ER_GPIO); also elsewhere on the board
PHY_TX0: U4.38 (TX_D0); also elsewhere on the board
PHY_TX1: U4.37 (TX_D1); also elsewhere on the board
PHY_TX2: U4.36 (TX_D2); also elsewhere on the board
PHY_TX3: U4.35 (TX_D3); also elsewhere on the board
PHY_TX4: U4.34 (TX_D4); also elsewhere on the board
PHY_TX5: U4.33 (TX_D5); also elsewhere on the board
PHY_TX6: U4.32 (TX_D6); also elsewhere on the board
PHY_TX7: U4.31 (TX_D7); also elsewhere on the board
PHY_TXCK: U4.40 (GTX_CLK); also elsewhere on the board
PHY_TXCK_10/100: U4.30 (TX_CLK); also elsewhere on the board
PHY_TXCTL_DV: U4.52 (TX_EN_TX_CTRL); also elsewhere on the board
PHY_TX_ER: U4.39 (TX_ER); also elsewhere on the board
POE+_MODE_A: C10.2, T1.22 (24); also elsewhere on the board
POE+_MODE_B: C14.2, T1.16 (18); also elsewhere on the board
POE-_MODE_A: C12.2, T1.21; also elsewhere on the board
POE-_MODE_B: C17.2, T1.15; also elsewhere on the board
VDDA1P8: U4.64 (VDDA1P8)
VDDA1P8_2: U4.17 (VDDA1P8_2)

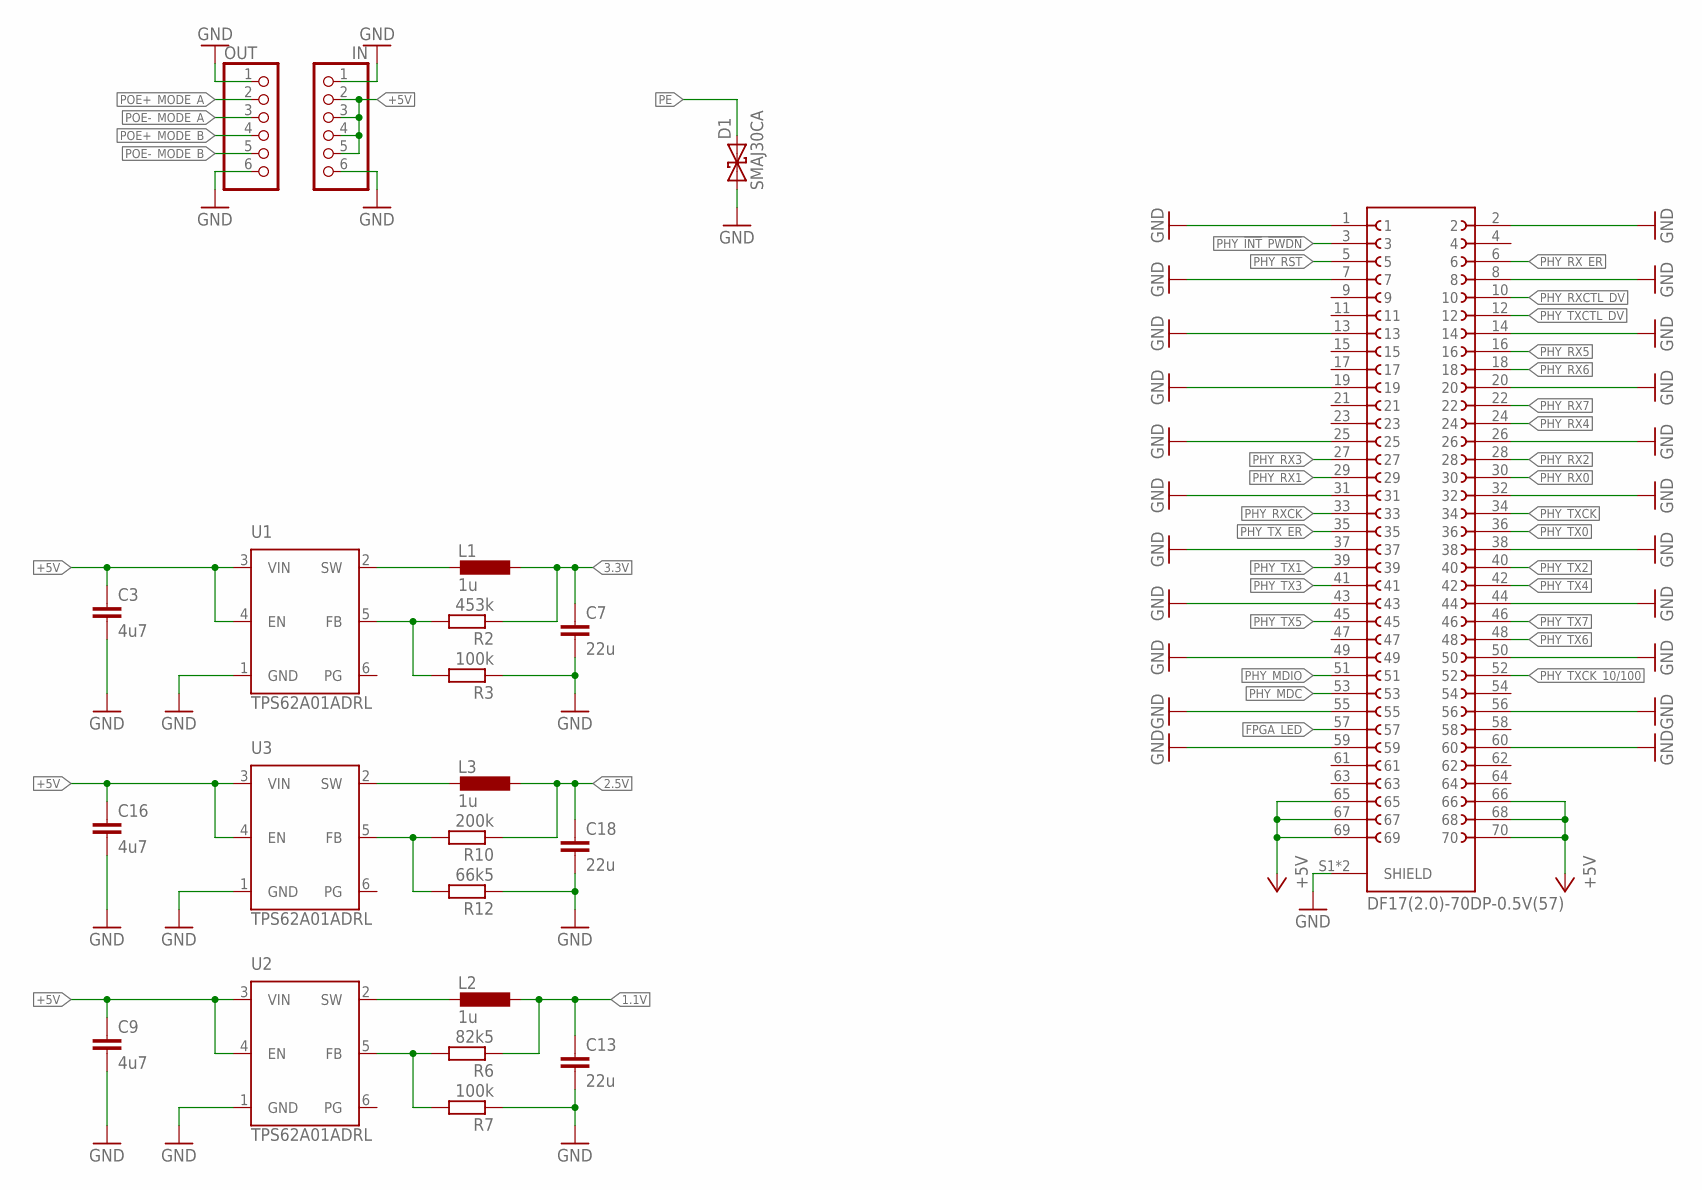
[picture p69: schematic Interface_ETH.sch, sheet 2, Power]

Parts:
C3, C9, C16: 4u7; C0603; LCSC C19666
C7, C13, C18: 22u; C0603; LCSC C109448
D1: SMAJ30CA; DO214AC; FARNELL 1827672
IN: PINHD-1X06_2.00; 1X06M
J1: DF17(2.0)-70DP-0.5V(57)
L1, L2, L3: 1u; L1008; MPN LQM2HPN1R0MG0L; DIGIKEY 490-5112-1-ND
OUT: PINHD-1X06_2.00; 1X06M
R2: 453k; R0402; LCSC C137978
R3: 100k; R0402; DIGIKEY RMCF0402FT100KCT-ND
R6: 82k5; R0402; DIGIKEY RMCF0402FT66K5CT-ND
R7: 100k; R0402; LCSC C60491
R10: 200k; R0402; LCSC C137978
R12: 66k5; R0402; DIGIKEY RMCF0402FT100KCT-ND
U1, U2, U3: TPS62A01ADRL; SOTFL50P160X60-6N; DIGIKEY 296-TPS62A01ADRLRCT-ND

Connections:
1.1V: C13.1, L2.1, R6.1; also elsewhere on the board
2.5V: C18.1, L3.1, R10.1; also elsewhere on the board
3.3V: C7.1, L1.1, R2.1; also elsewhere on the board
+5V: C3.1, C9.1, C16.1, IN.2, IN.3, IN.4, IN.5, J1.65, J1.66, J1.67, J1.68, J1.69, J1.70, U1.3 (VIN), U1.4 (EN), U2.3 (VIN), U2.4 (EN), U3.3 (VIN), U3.4 (EN)
FPGA_LED: J1.57; also elsewhere on the board
GND: C3.2, C7.2, C9.2, C13.2, C16.2, C18.2, D1.A (1), IN.1, IN.6, J1.1, J1.2, J1.7, J1.8, J1.13, J1.14, J1.19, J1.20, J1.25, J1.26, J1.31, J1.32, J1.37, J1.38, J1.43, J1.44, J1.49, J1.50, J1.55, J1.56, J1.59, J1.60, J1.S1 (SHIELD), J1.S2 (SHIELD), OUT.1, OUT.6, R3.1, R7.1, R12.1, U1.1 (GND), U2.1 (GND), U3.1 (GND); also elsewhere on the board
unnamed: L2.2, U2.2 (SW)
unnamed: L1.2, U1.2 (SW)
unnamed: L3.2, U3.2 (SW)
unnamed: R10.2, R12.2, U3.5 (FB)
unnamed: R6.2, R7.2, U2.5 (FB)
unnamed: R2.2, R3.2, U1.5 (FB)
PE: D1.C (2); also elsewhere on the board
PHY_!INT!_!PWDN: J1.3; also elsewhere on the board
PHY_MDC: J1.53; also elsewhere on the board
PHY_MDIO: J1.51; also elsewhere on the board
PHY_RST: J1.5; also elsewhere on the board
PHY_RX0: J1.30; also elsewhere on the board
PHY_RX1: J1.29; also elsewhere on the board
PHY_RX2: J1.28; also elsewhere on the board
PHY_RX3: J1.27; also elsewhere on the board
PHY_RX4: J1.24; also elsewhere on the board
PHY_RX5: J1.16; also elsewhere on the board
PHY_RX6: J1.18; also elsewhere on the board
PHY_RX7: J1.22; also elsewhere on the board
PHY_RXCK: J1.33; also elsewhere on the board
PHY_RXCTL_DV: J1.10; also elsewhere on the board
PHY_RX_ER: J1.6; also elsewhere on the board
PHY_TX0: J1.36; also elsewhere on the board
PHY_TX1: J1.39; also elsewhere on the board
PHY_TX2: J1.40; also elsewhere on the board
PHY_TX3: J1.41; also elsewhere on the board
PHY_TX4: J1.42; also elsewhere on the board
PHY_TX5: J1.45; also elsewhere on the board
PHY_TX6: J1.48; also elsewhere on the board
PHY_TX7: J1.46; also elsewhere on the board
PHY_TXCK: J1.34; also elsewhere on the board
PHY_TXCK_10/100: J1.52; also elsewhere on the board
PHY_TXCTL_DV: J1.12; also elsewhere on the board
PHY_TX_ER: J1.35; also elsewhere on the board
POE+_MODE_A: OUT.2; also elsewhere on the board
POE+_MODE_B: OUT.4; also elsewhere on the board
POE-_MODE_A: OUT.3; also elsewhere on the board
POE-_MODE_B: OUT.5; also elsewhere on the board
