stdlogicvector/modularCamera_hw/Interface_ETH.brd

## EAGLE design Interface_ETH.brd (continued)

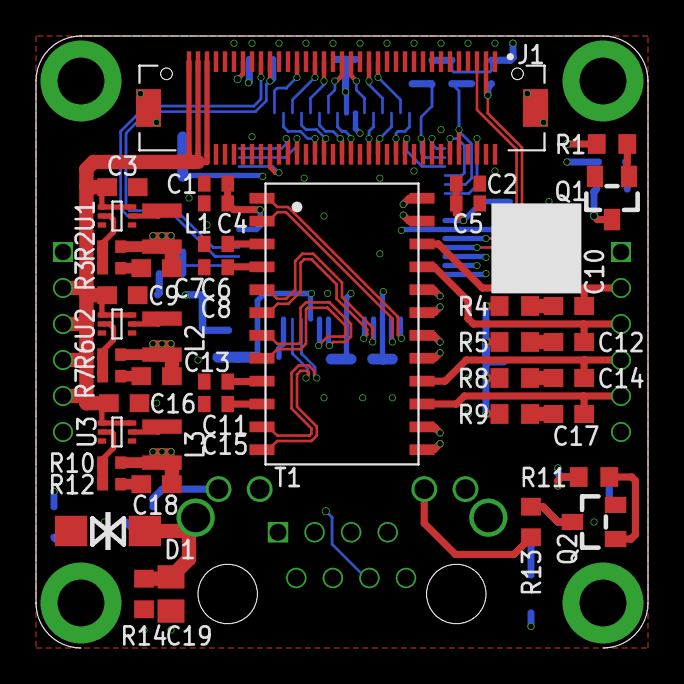
[picture p70: board Interface_ETH.brd from above]

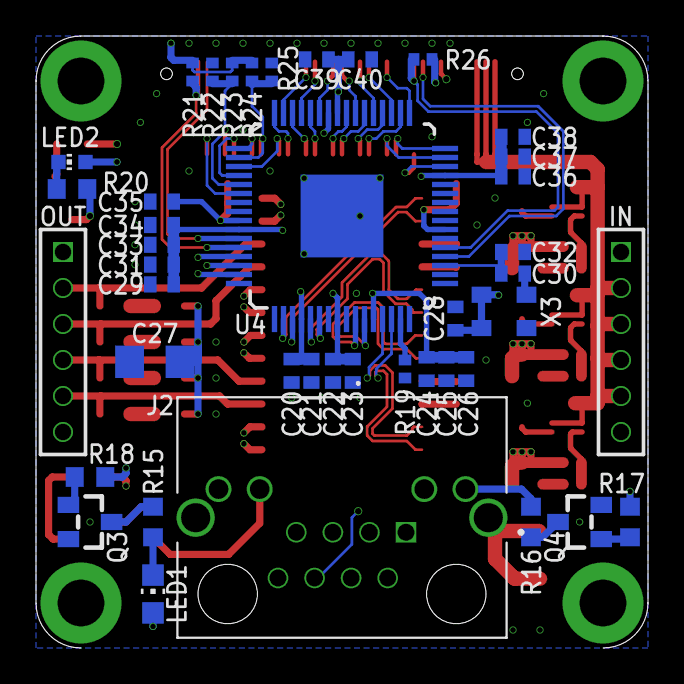
[picture p71: board Interface_ETH.brd from below]

Board: 4 copper layers, 34.0 x 34.0 mm, 86 parts (42 on the bottom side), 87 nets.
